EnnoidMe/ENNOID-BMS/Master/LV/PCB/CAD/AMC1301.step

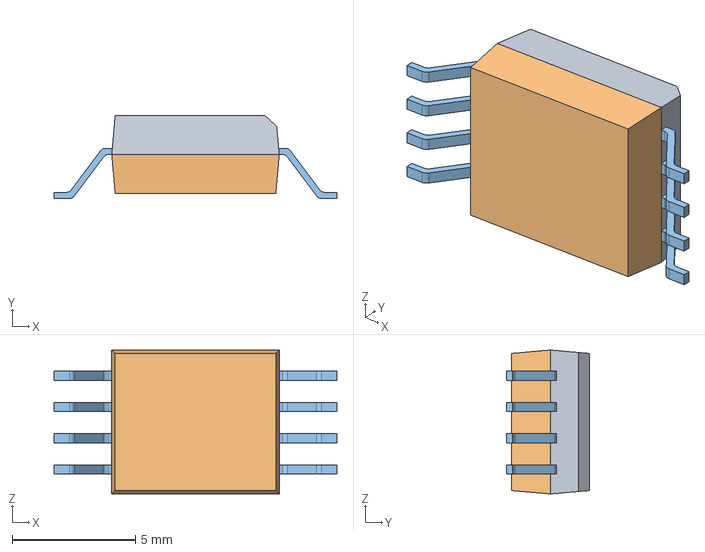
[picture p14: CAD file, 2019-01-14]
Master/LV/PCB/CAD/AMC1301.step
11.5 x 3.38 x 5.85 mm
