EnnoidMe/ENNOID-BMS/Master/LV/PCB/CAD/BAS-M-R0002.step

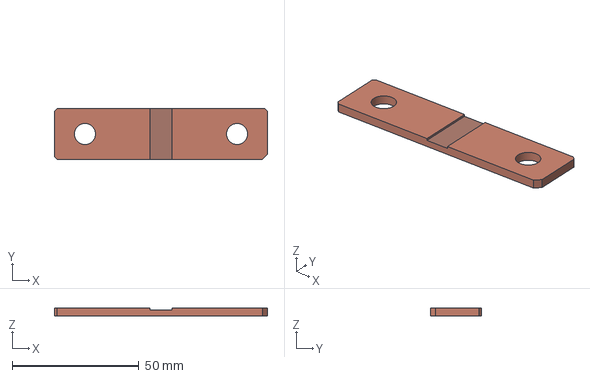
[picture p15: CAD file, 2018-12-30]
Master/LV/PCB/CAD/BAS-M-R0002.step
84.0 x 20.0 x 3.00 mm
