EnnoidMe/ENNOID-BMS/Master/HV/PCB/BMS-Master.sch

## KiCad design Master/HV/PCB/BMS-Master.sch (2020-04-05)

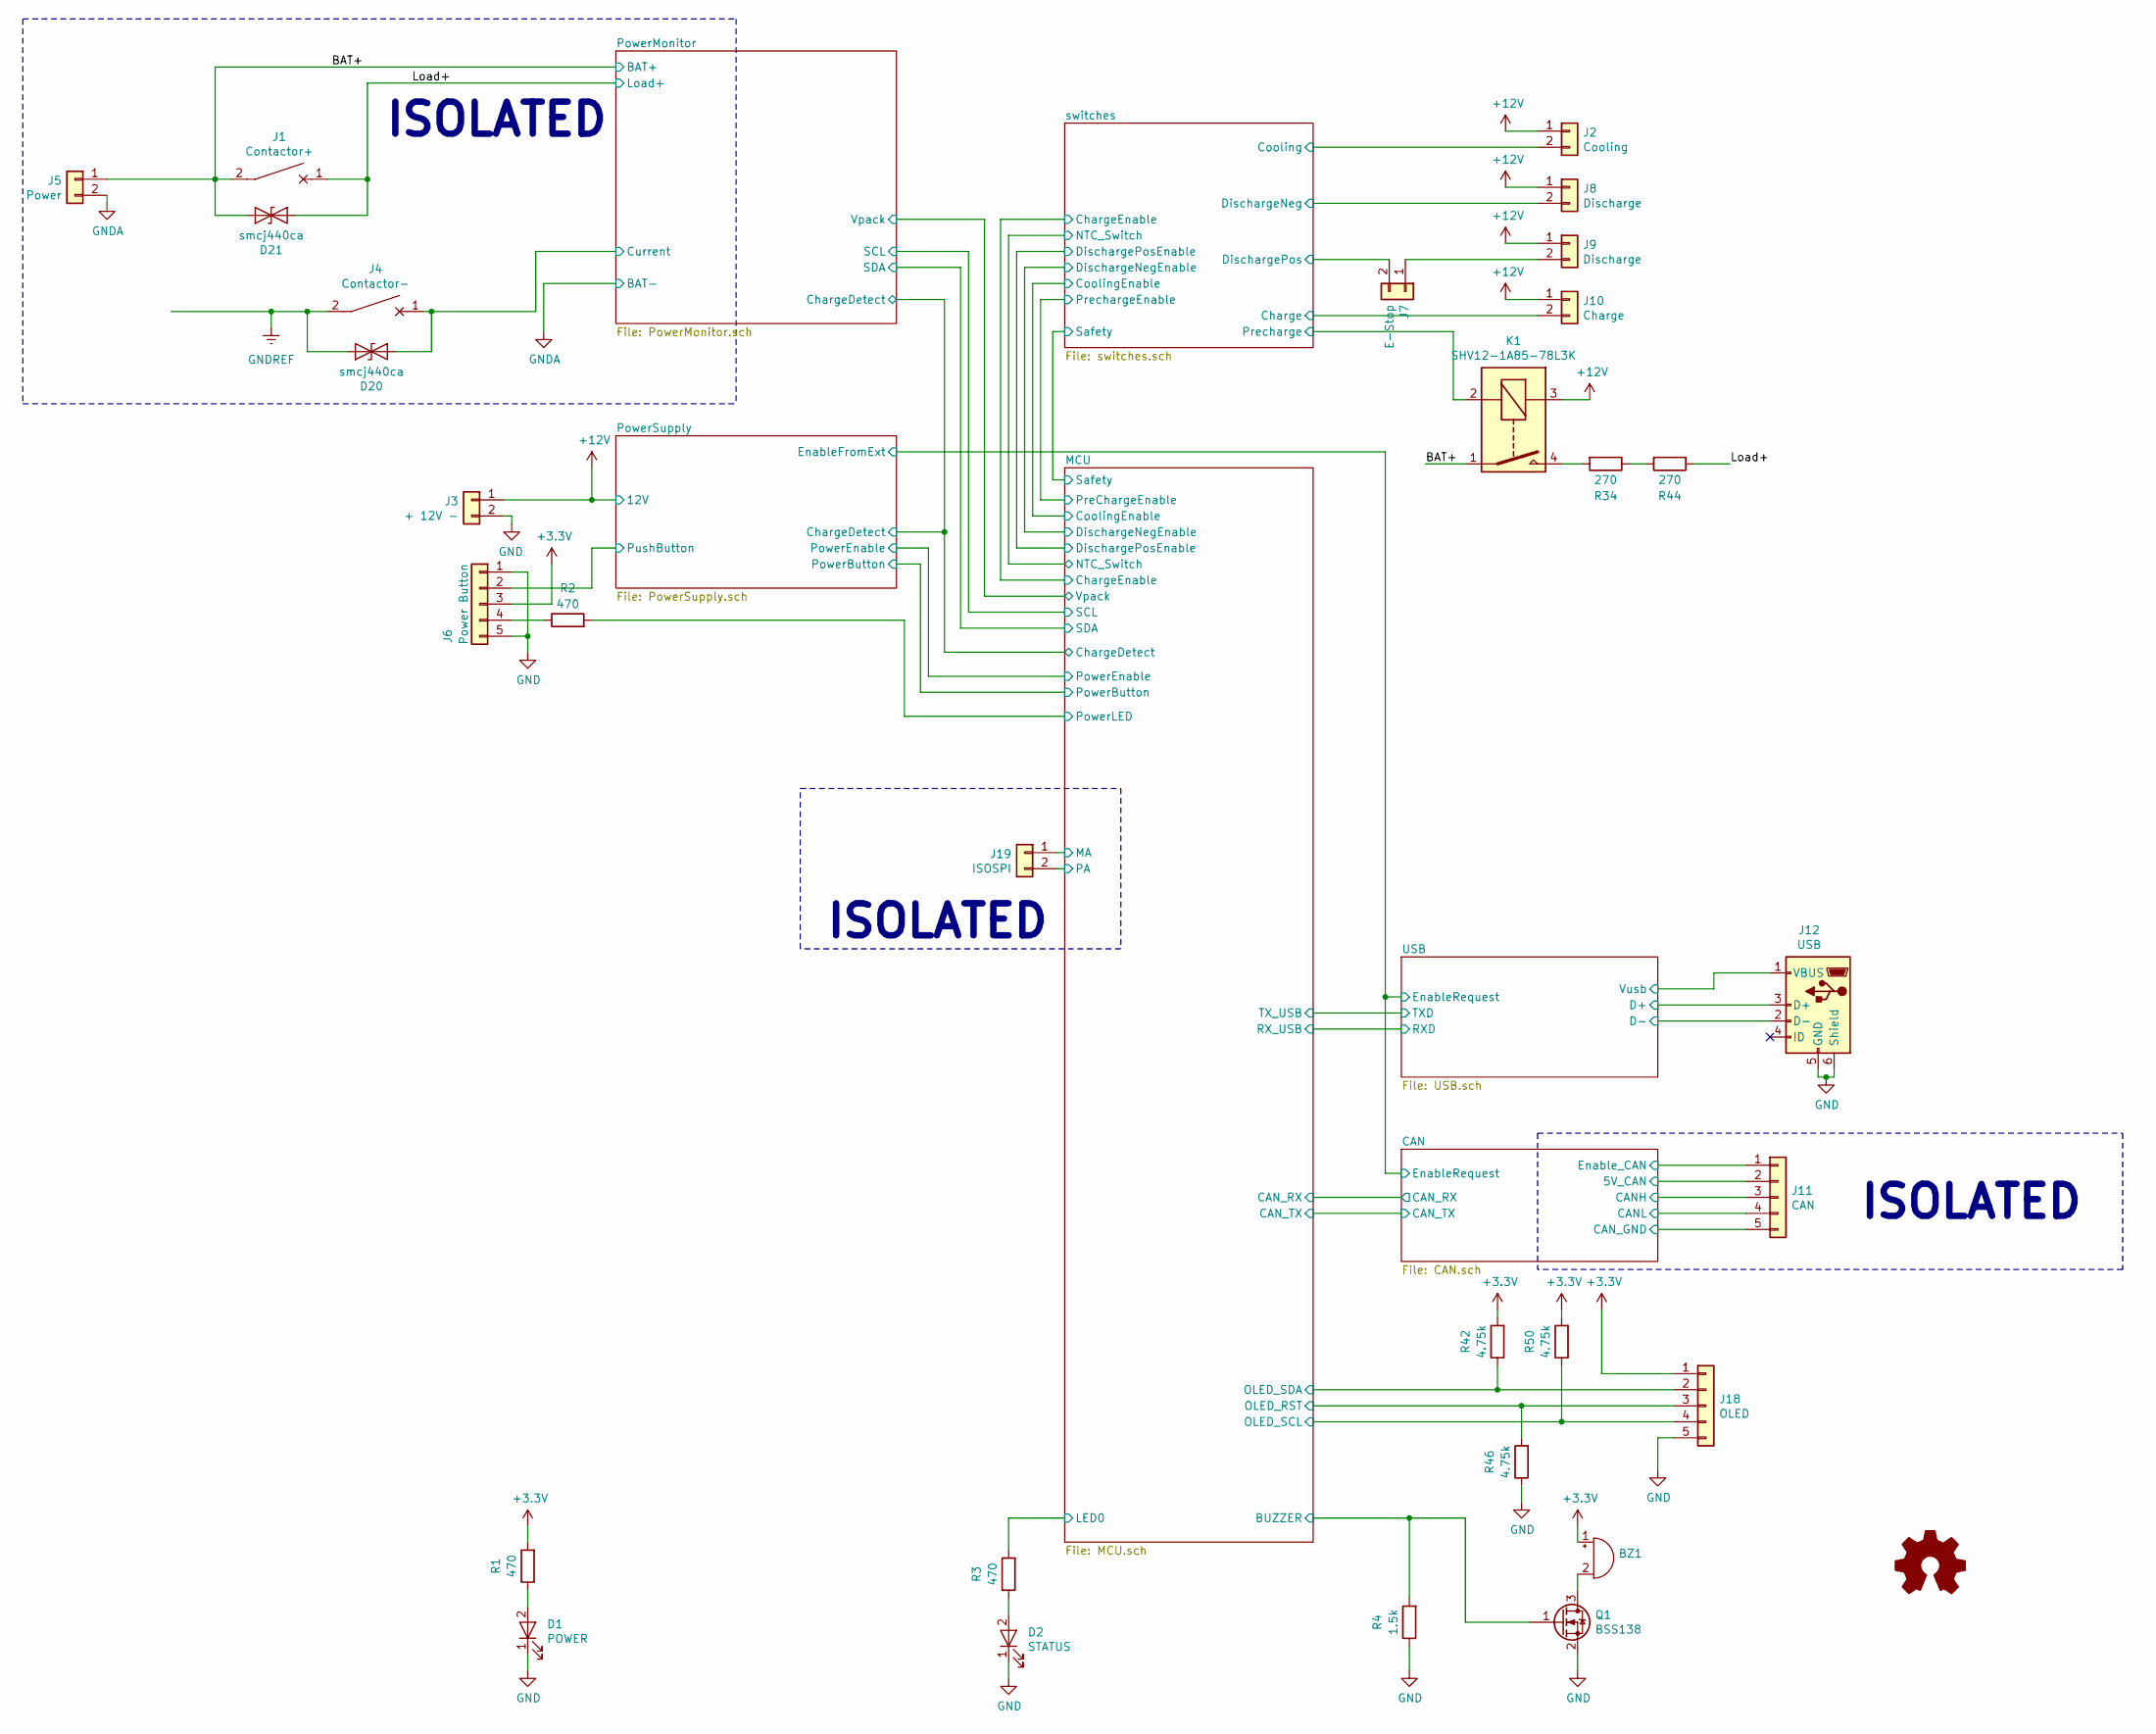
[picture p17: schematic BMS-Master.sch]

Parts:
BZ1: AI-1027-TWT-5V; BUZZER; MPN AI-1027-TWT-5V-2-R
D1: POWER; LED_0603_1608Metric; MPN SML-D12P8WT86C
D2: STATUS; LED_0603_1608Metric; MPN SML-D12P8WT86C
D20, D21: smcj440ca; D_SMC; MPN smcj440ca
J1: Contactor+; EVC500; MPN N/A
J2: Cooling; Pin_1x02-XL; MPN 70543-0001
J3: + 12V -; Pin_1x02-XL; MPN 70543-0001
J4: Contactor-; EVC500; MPN N/A
J5: Power; PhoenixContact_GMSTBVA_2,5_2-G_1x02_P7.50mm_Vertical; MPN 30.102
J6: Power Button; Molex_KK-6410-05_05x2.54mm_Straight; MPN 282834-5
J7: E-Stop; Pin_1x02-XL; MPN 70543-0001
J8, J9: Discharge; Pin_1x02-XL; MPN 70543-0001
J10: Charge; Pin_1x02-XL; MPN 70543-0001
J11: CAN; Molex_KK-6410-05_05x2.54mm_Straight; MPN 70543-0004
J12: USB; USB_Micro-B_Molex-105133-0001; MPN 47346-0001
J18: OLED; Molex_KK-6410-05_05x2.54mm_Straight; MPN 70543-0004
J19: ISOSPI; Pin_1x02-XL; MPN 70543-0001
K1: SHV12-1A85-78L3K; SHV12-1AB5-7BL3K
LOGO1: Logo_Open_Hardware_Small; ENNOID-LOGO; MPN N/A
Q1: BSS138; SOT-23; MPN BSS138
R1, R2, R3: 470; R_0603_1608Metric; MPN RC0603JR-07470RL
R4: 1.5k; R_0603_1608Metric; MPN RC0603JR-071K5L
R34, R44: 270; SM_3; MPN SMW3270RJT
R42, R46, R50: 4.75k; R_0603_1608Metric; MPN RC0603JR-074K7L

Connections:
5V_CAN: J11.2
+3.3V: BZ1.1 (-), J6.3, J18.1, R1.2, R42.2, R50.2
+12V: J2.1, J3.1, J8.1, J9.1, J10.1, K1.3
BAT+: D21.2 (A2), J1.2, J5.1, K1.1
BUZZER: Q1.1 (G), R4.2
CANH: J11.3
CANL: J11.4
CAN_GND: J11.5
Charge: J10.2
Cooling: J2.2
Current: D20.1 (A1), J4.1
D+: J12.3 (D+)
D-: J12.2 (D-)
DischargeNeg: J8.2
DischargePos: J7.2
Enable_CAN: J11.1
GND: D1.1 (K), D2.1 (K), J3.2, J6.1, J6.5, J12.5 (GND), J12.6 (Shield), J18.5, Q1.2 (S), R4.1, R46.1
GNDA: J5.2
GNDREF: D20.2 (A2), J4.2
LED0: R3.2
Load+: D21.1 (A1), J1.1, R44.1
MA: J19.1
unnamed: BZ1.2 (+), Q1.3 (D)
unnamed: D1.2 (A), R1.1
unnamed: D2.2 (A), R3.1
unnamed: J6.4, R2.1
unnamed: J7.1, J9.2
unnamed: K1.4, R34.2
unnamed: R34.1, R44.2
OLED_RST: J18.3, R46.2
OLED_SCL: J18.4, R50.1
OLED_SDA: J18.2, R42.1
PA: J19.2
PowerLED: R2.2
Precharge: K1.2
PushButton: J6.2
Vusb: J12.1 (VBUS)

Notes on the sheet:
ISOLATED
