EnnoidMe/ENNOID-BMS/Master/HV/PCB/MCU.sch

## KiCad design Master/HV/PCB/MCU.sch (2020-03-30)

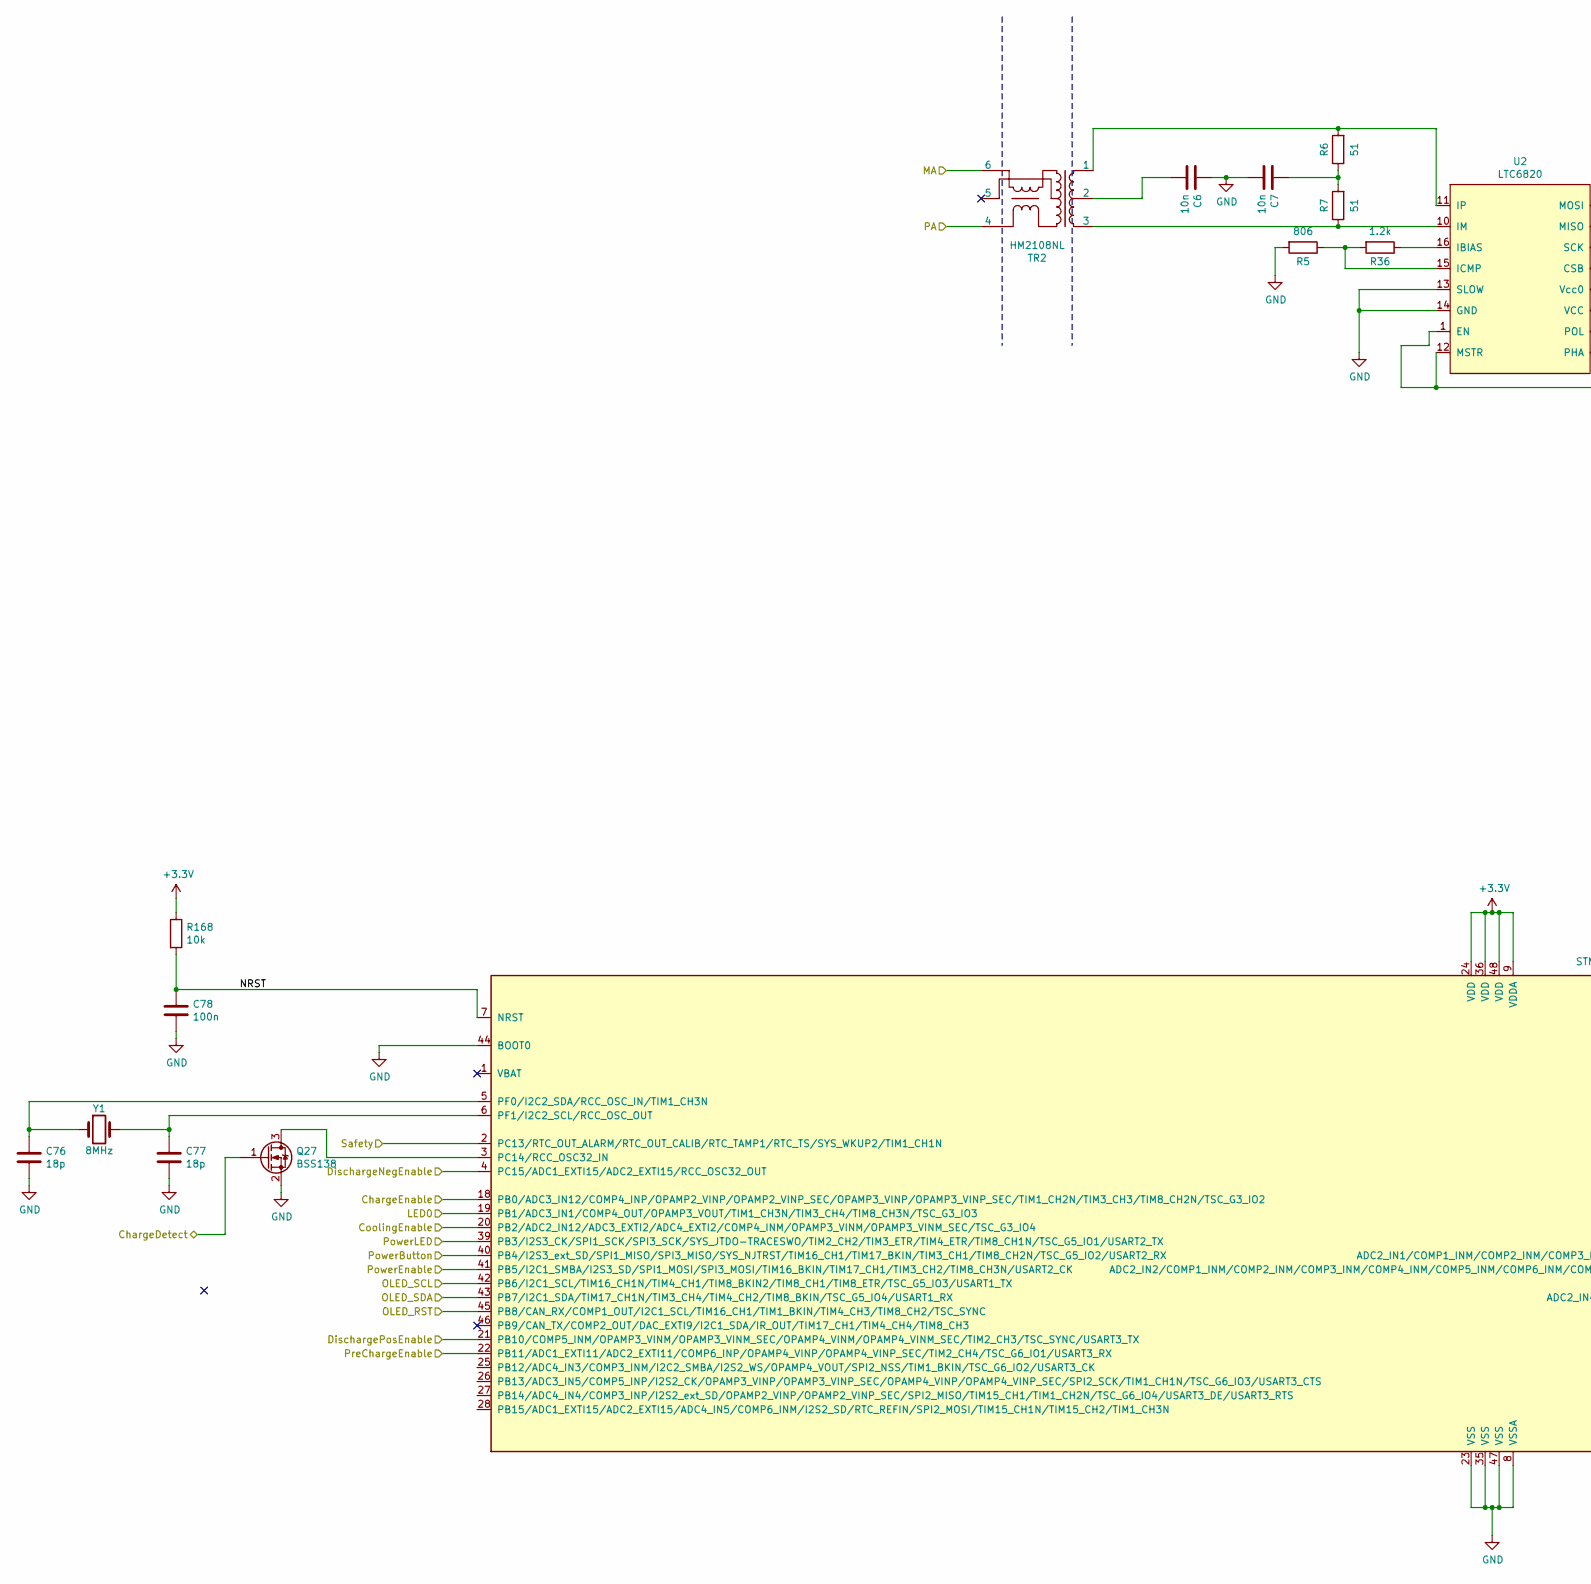
[picture p19: schematic MCU.sch, part in row 1, column 1]

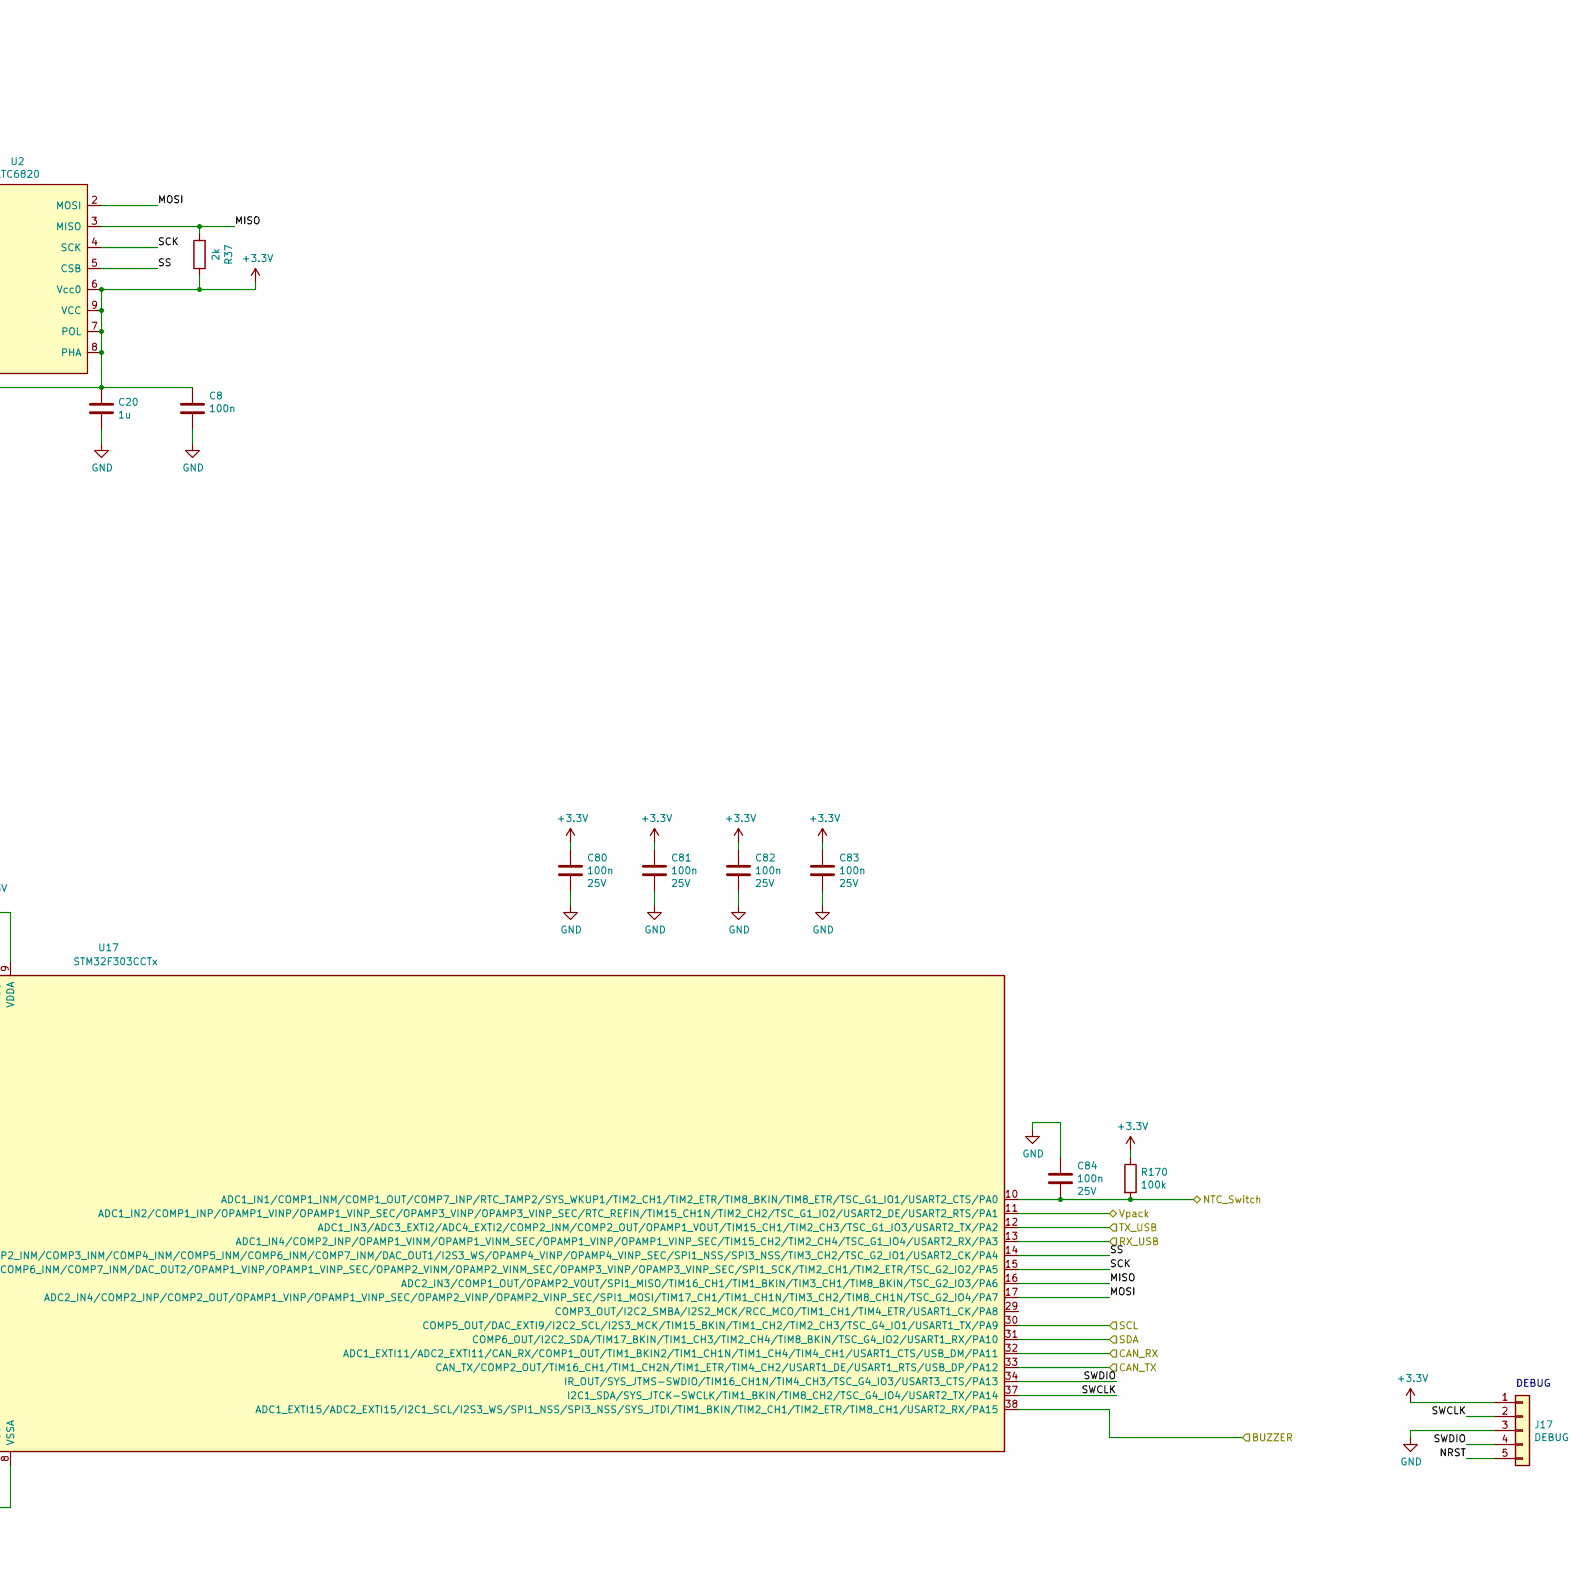
[picture p20: schematic MCU.sch, part in row 1, column 2]

Parts:
C6, C7: 10n; C_0603_1608Metric; MPN GRM188R71H103KA01D
C8, C80, C81, C82, C83, C84: 100n; C_0603_1608Metric; Voltage 25V; MPN GRM188R71E104KA01D
C20: 1u; C_0603_1608Metric; MPN GRM188R71E105KA12D
C76, C77: 18p; C_0603_1608Metric; Voltage 50V; MPN GRM1885C1H180JA01D
C78: 100n; C_0603_1608Metric; MPN GRM188R71E104KA01D
J17: DEBUG; Molex_PicoBlade_53398-0571_1x05-1MP_P1.25mm_Vertical; MPN 53398-0571
Q27: BSS138; SOT-23; MPN BSS138
R5: 806; R_0603_1608Metric; MPN RC0603FR-07806RL
R6, R7: 51; R_0603_1608Metric; MPN RC0603JR-0751RL
R36: 1.2k; R_0603_1608Metric; MPN RC0603JR-071K2L
R37: 2k; R_0603_1608Metric; MPN RC0603FR-072KL
R168: 10k; R_0603_1608Metric; MPN RC0603FR-0710KL
R170: 100k; R_0603_1608Metric; MPN RC0603JR-07100KL
TR2: HM2108NL; MPN HM2108NL
U2: LTC6820; MSOP-16_3x4mm_Pitch0.5mm; MPN LTC6820IMS#PBF
U17: STM32F303CCTx; LQFP-48_7x7mm_Pitch0.5mm; MPN STM32F303CCT6
Y1: 8MHz; Crystal_SMD_Abracon_ABM3-2pin_5.0x3.2mm; MPN ABM3-8.000MHZ-D2Y-T

Connections:
+3.3V: C8.1, C20.2, C80.1, C81.1, C82.1, C83.1, J17.1, R37.1, R168.1, R170.1, U2.1 (EN), U2.6 (Vcc0), U2.7 (POL), U2.8 (PHA), U2.9 (VCC), U2.12 (MSTR), U17.9 (VDDA), U17.24 (VDD), U17.36 (VDD), U17.48 (VDD)
BUZZER: U17.38 (ADC1_EXTI15/ADC2_EXTI15/I2C1_SCL/I2S3_W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)
CAN_RX: U17.32 (ADC1_EXTI11/ADC2_EXTI11/CAN_RX/COMP1_OU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)
CAN_TX: U17.33 (CAN_TX/COMP2_OUT/TIM16_CH1/TIM1_CH2N/TI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)
ChargeDetect: Q27.1 (G)
ChargeEnable: U17.18 (PB0/ADC3_IN12/COMP4_INP/OPAMP2_VINP/OPA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)
CoolingEnable: U17.20 (PB2/ADC2_IN12/ADC3_EXTI2/ADC4_EXTI2/COM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)
DischargeNegEnable: U17.4 (PC15/ADC1_EXTI15/ADC2_EXTI15/RCC_OSC32_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)
DischargePosEnable: U17.21 (PB10/COMP5_INM/OPAMP3_VINM/OPAMP3_VINM_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)
GND: C6.2, C7.1, C8.2, C20.1, C76.2, C77.2, C78.2, C80.2, C81.2, C82.2, C83.2, C84.1, J17.3, Q27.2 (S), R5.2, U2.13 (SLOW), U2.14 (GND), U17.8 (VSSA), U17.23 (VSS), U17.35 (VSS), U17.44 (BOOT0), U17.47 (VSS)
LED0: U17.19 (PB1/ADC3_IN1/COMP4_OUT/OPAMP3_VOUT/TIM1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)
MA: TR2.6
MISO: R37.2, U2.3 (MISO), U17.16 (ADC2_IN3/COMP1_OUT/OPAMP2_VOUT/SPI1_MIS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)
MOSI: U2.2 (MOSI), U17.17 (ADC2_IN4/COMP2_INP/COMP2_OUT/OPAMP1_VIN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)
NRST: C78.1, J17.5, R168.2, U17.7 (NRST)
NTC_Switch: C84.2, R170.2, U17.10 (ADC1_IN1/COMP1_INM/COMP1_OUT/COMP7_INP/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)
unnamed: C6.1, TR2.2
unnamed: C7.2, R6.1, R7.2
unnamed: C76.1, U17.5 (PF0/I2C2_SDA/RCC_OSC_IN/TIM1_CH3N), Y1.1
unnamed: C77.1, U17.6 (PF1/I2C2_SCL/RCC_OSC_OUT), Y1.2
unnamed: Q27.3 (D), U17.3 (PC14/RCC_OSC32_IN)
unnamed: R6.2, TR2.1, U2.11 (IP)
unnamed: R7.1, TR2.3, U2.10 (IM)
unnamed: R36.1, U2.16 (IBIAS)
unnamed: R5.1, R36.2, U2.15 (ICMP)
OLED_RST: U17.45 (PB8/CAN_RX/COMP1_OUT/I2C1_SCL/TIM16_CH1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)
OLED_SCL: U17.42 (PB6/I2C1_SCL/TIM16_CH1N/TIM4_CH1/TIM8_B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)
OLED_SDA: U17.43 (PB7/I2C1_SDA/TIM17_CH1N/TIM3_CH4/TIM4_C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)
PA: TR2.4
PowerButton: U17.40 (PB4/I2S3_ext_SD/SPI1_MISO/SPI3_MISO/SYS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)
PowerEnable: U17.41 (PB5/I2C1_SMBA/I2S3_SD/SPI1_MOSI/SPI3_MO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)
PowerLED: U17.39 (PB3/I2S3_CK/SPI1_SCK/SPI3_SCK/SYS_JTDO-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)
PreChargeEnable: U17.22 (PB11/ADC1_EXTI11/ADC2_EXTI11/COMP6_INP/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)
RX_USB: U17.13 (ADC1_IN4/COMP2_INP/OPAMP1_VINM/OPAMP1_V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)
SCK: U2.4 (SCK), U17.15 (ADC2_IN2/COMP1_INM/COMP2_INM/COMP3_INM/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)
SCL: U17.30 (COMP5_OUT/DAC_EXTI9/I2C2_SCL/I2S3_MCK/T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)
SDA: U17.31 (COMP6_OUT/I2C2_SDA/TIM17_BKIN/TIM1_CH3/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)
SS: U2.5 (CSB), U17.14 (ADC2_IN1/COMP1_INM/COMP2_INM/COMP3_INM/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)
SWCLK: J17.2, U17.37 (I2C1_SDA/SYS_JTCK-SWCLK/TIM1_BKIN/TIM8_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)
SWDIO: J17.4, U17.34 (IR_OUT/SYS_JTMS-SWDIO/TIM16_CH1N/TIM4_C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)
Safety: U17.2 (PC13/RTC_OUT_ALARM/RTC_OUT_CALIB/RTC_TA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)
TX_USB: U17.12 (ADC1_IN3/ADC3_EXTI2/ADC4_EXTI2/COMP2_IN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)
Vpack: U17.11 (ADC1_IN2/COMP1_INP/OPAMP1_VINP/OPAMP1_V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)

Notes on the sheet:
DEBUG
