EnnoidMe/ENNOID-BMS/Master/HV/PCB/PowerMonitor.sch

## KiCad design Master/HV/PCB/PowerMonitor.sch (2020-04-05)

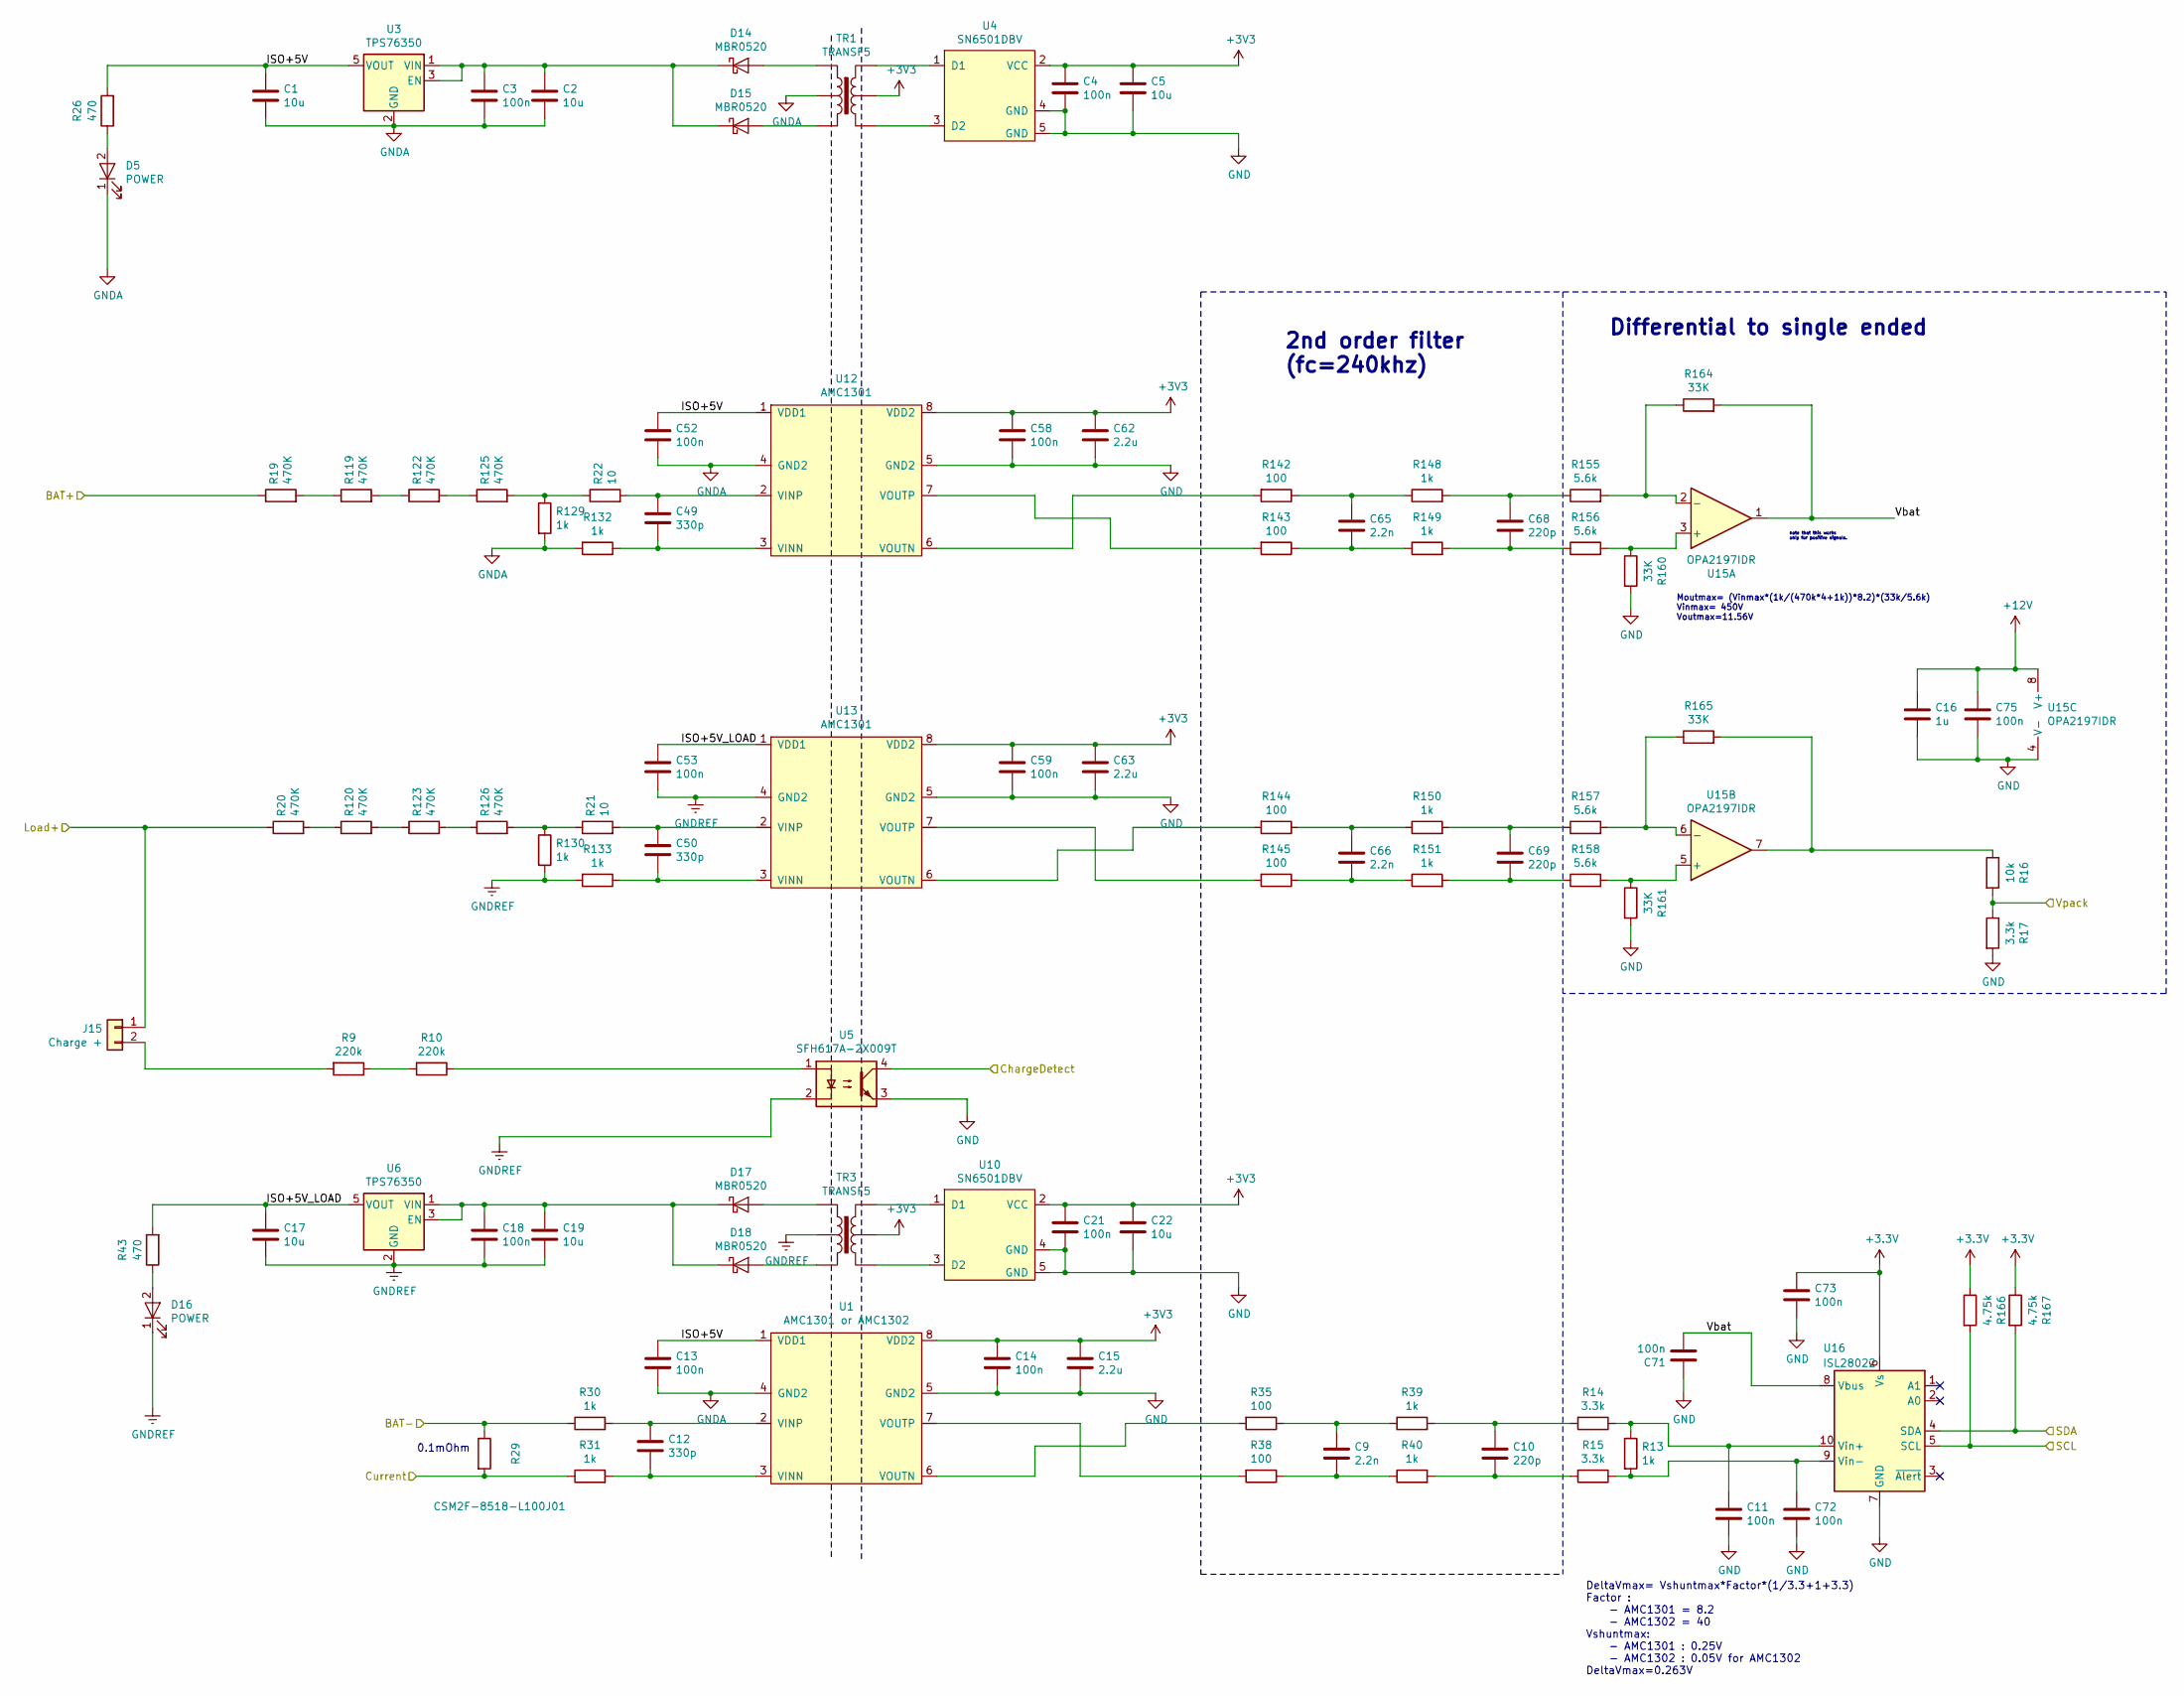
[picture p21: schematic PowerMonitor.sch]

Parts:
C1, C2, C17, C19: 10u; C_0805_2012Metric; MPN CL21A106KAYNNNE
C3, C4, C11, C13, C14, C18, C21, C52, C53, C58, C59, C71, C72, C73, C75: 100n; C_0603_1608Metric; MPN GRM188R71E104KA01D
C5, C22: 10u; C_0603_1608Metric; MPN CL10A106MQ8NNNC
C9, C65, C66: 2.2n; C_0603_1608Metric; MPN GRM1885C1H222JA01D
C10, C68, C69: 220p; C_0603_1608Metric; MPN GRM1555C1H221JA01D
C12, C49, C50: 330p; C_0603_1608Metric; MPN CL10B331KB8NNNC
C15, C62, C63: 2.2u; C_0603_1608Metric; MPN GRM188R61A225KE34D
C16: 1u; C_0603_1608Metric; MPN GRM188R71E105KA12D
D5, D16: POWER; LED_0603_1608Metric; MPN SML-D12P8WT86C
D14, D15, D17, D18: MBR0520; D_SOD-123; MPN MBR0502L
J15: Charge +; PhoenixContact_GMSTBVA_2,5_2-G_1x02_P7.50mm_Vertical; MPN 30.102
R9, R10: 220k; R_2512_6332Metric; MPN 25121WF2203T4E
R13, R30, R31, R39, R40, R129, R130, R132, R133, R148, R149, R150, R151: 1k; R_0603_1608Metric; MPN MCR03EZPFX1001
R14, R15, R17: 3.3k; R_0603_1608Metric; MPN RC0603FR-073K3L
R16: 10k; R_0603_1608Metric; MPN RC0603FR-0710KL
R19, R20, R119, R120, R122, R123, R125, R126: 470K; R_1206_3216Metric; MPN RC1206FR-07470KL
R21, R22: 10; R_0603_1608Metric; MPN RC0603JR-0710RL
R26, R43: 470; R_0603_1608Metric; MPN RC0603JR-07470RL
R29: CSM2F-8518-L100J01; MPN CSM2F-8518-L100J01
R35, R38, R142, R143, R144, R145: 100; R_0603_1608Metric; MPN RC0603FR-07100RL
R155, R156, R157, R158: 5.6k; R_0603_1608Metric; MPN RC0603JR-075K6L
R160, R161, R164, R165: 33K; R_0603_1608Metric; MPN RC0603FR-0733KL
R166, R167: 4.75k; R_0603_1608Metric; MPN RC0603JR-074K7L
TR1, TR3: TRANSF5; WURTH-760390014; MPN 760390014
U1: AMC1301 or AMC1302; SSO-8_6.8x5.9mm_Pitch1.27mm_Clearance8mm; MPN AMC1301DWV
U3, U6: TPS76350; SOT-23-5; MPN TPS76350DBVR
U4, U10: SN6501DBV; SOT-23-5; MPN SN6501DBVR
U5: SFH617A-2X009T; SMDIP-4_W9.53mm_Clearance8mm; MPN SFH617A-2X009T
U12, U13: AMC1301; SSO-8_6.8x5.9mm_Pitch1.27mm_Clearance8mm; MPN AMC1301DWV
U15: OPA2197IDR; SOIC-8_3.9x4.9mm_Pitch1.27mm; MPN OPA2197IDR
U16: ISL28022; MSOP-10_3x3mm_Pitch0.5mm; MPN ISL28022FUZ-T7A

Connections:
+3.3V: C73.2, R166.1, R167.1, U16.6 (Vs)
+3V3: C4.1, C5.1, C14.1, C15.1, C21.1, C22.1, C58.1, C59.1, C62.1, C63.1, TR1.5, TR3.5, U1.8 (VDD2), U4.2 (VCC), U10.2 (VCC), U12.8 (VDD2), U13.8 (VDD2)
+12V: C16.1, C75.1, U15.8 (V+)
BAT+: R19.1
BAT-: R29.1, R30.1
ChargeDetect: U5.4
Current: R29.2, R31.1
GND: C4.2, C5.2, C11.1, C14.2, C15.2, C16.2, C21.2, C22.2, C58.2, C59.2, C62.2, C63.2, C71.2, C72.1, C73.1, C75.2, R17.2, R160.2, R161.2, U1.5 (GND2), U4.4 (GND), U4.5 (GND), U5.3, U10.4 (GND), U10.5 (GND), U12.5 (GND2), U13.5 (GND2), U15.4 (V-), U16.7 (GND)
GNDA: C1.2, C2.2, C3.2, C13.2, C52.2, D5.1 (K), R129.2, R132.2, TR1.2, U1.4 (GND2), U3.2 (GND), U12.4 (GND2)
GNDREF: C17.2, C18.2, C19.2, C53.2, D16.1 (K), R130.2, R133.2, TR3.2, U5.2, U6.2 (GND), U13.4 (GND2)
ISO+5V: C1.1, C13.1, C52.1, R26.2, U1.1 (VDD1), U3.5 (VOUT), U12.1 (VDD1)
ISO+5V_LOAD: C17.1, C53.1, R43.2, U6.5 (VOUT), U13.1 (VDD1)
Load+: J15.1, R20.1
unnamed: C2.1, C3.1, D14.1 (K), D15.1 (K), U3.1 (VIN), U3.3 (EN)
unnamed: C9.1, R35.1, R39.1
unnamed: C9.2, R38.1, R40.1
unnamed: C10.1, R14.2, R39.2
unnamed: C10.2, R15.2, R40.2
unnamed: C11.2, R13.1, R14.1, U16.10 (Vin+)
unnamed: C12.1, R30.2, U1.2 (VINP)
unnamed: C12.2, R31.2, U1.3 (VINN)
unnamed: C18.1, C19.1, D17.1 (K), D18.1 (K), U6.1 (VIN), U6.3 (EN)
unnamed: C49.1, R22.2, U12.2 (VINP)
unnamed: C49.2, R132.1, U12.3 (VINN)
unnamed: C50.1, R21.2, U13.2 (VINP)
unnamed: C50.2, R133.1, U13.3 (VINN)
unnamed: C65.1, R142.1, R148.1
unnamed: C65.2, R143.1, R149.1
unnamed: C66.1, R144.1, R150.1
unnamed: C66.2, R145.1, R151.1
unnamed: C68.1, R148.2, R155.1
unnamed: C68.2, R149.2, R156.1
unnamed: C69.1, R150.2, R157.1
unnamed: C69.2, R151.2, R158.1
unnamed: C72.2, R13.2, R15.1, U16.9 (Vin-)
unnamed: D5.2 (A), R26.1
unnamed: D14.2 (A), TR1.1
unnamed: D15.2 (A), TR1.3
unnamed: D16.2 (A), R43.1
unnamed: D17.2 (A), TR3.1
unnamed: D18.2 (A), TR3.3
unnamed: J15.2, R9.2
unnamed: R10.1, U5.1
unnamed: R9.1, R10.2
unnamed: R16.1, R165.2, U15.7
unnamed: R35.2, U1.6 (VOUTN)
unnamed: R38.2, U1.7 (VOUTP)
unnamed: R19.2, R119.1
unnamed: R119.2, R122.1
unnamed: R20.2, R120.1
unnamed: R120.2, R123.1
unnamed: R122.2, R125.1
unnamed: R123.2, R126.1
unnamed: R22.1, R125.2, R129.1
unnamed: R21.1, R126.2, R130.1
unnamed: R142.2, U12.6 (VOUTN)
unnamed: R143.2, U12.7 (VOUTP)
unnamed: R144.2, U13.6 (VOUTN)
unnamed: R145.2, U13.7 (VOUTP)
unnamed: R155.2, R164.1, U15.2 (-)
unnamed: R156.2, R160.1, U15.3 (+)
unnamed: R157.2, R165.1, U15.6 (-)
unnamed: R158.2, R161.1, U15.5 (+)
unnamed: TR1.4, U4.3 (D2)
unnamed: TR1.6, U4.1 (D1)
unnamed: TR3.4, U10.3 (D2)
unnamed: TR3.6, U10.1 (D1)
SCL: R166.2, U16.5 (SCL)
SDA: R167.2, U16.4 (SDA)
Vbat: C71.1, R164.2, U15.1, U16.8 (Vbus)
Vpack: R16.2, R17.1

Notes on the sheet:
Differential to single ended
note that this works only for positive signals.
2nd order filter (fc=240khz)
0.1mOhm
Moutmax= (Vinmax*(1k/(470k*4+1k))*8.2)*(33k/5.6k) Vinmax= 450V Voutmax=11.56V
DeltaVmax= Vshuntmax*Factor*(1/3.3+1+3.3) Factor : - AMC1301 = 8.2 - AMC1302 = 40 Vshuntmax: - AMC1301 : 0.25V - AMC1302 : 0.05V for AMC1302 DeltaVmax=0.263V
