EnnoidMe/ENNOID-BMS/Master/HV/PCB/PowerSupply.sch

## KiCad design Master/HV/PCB/PowerSupply.sch (2020-03-01)

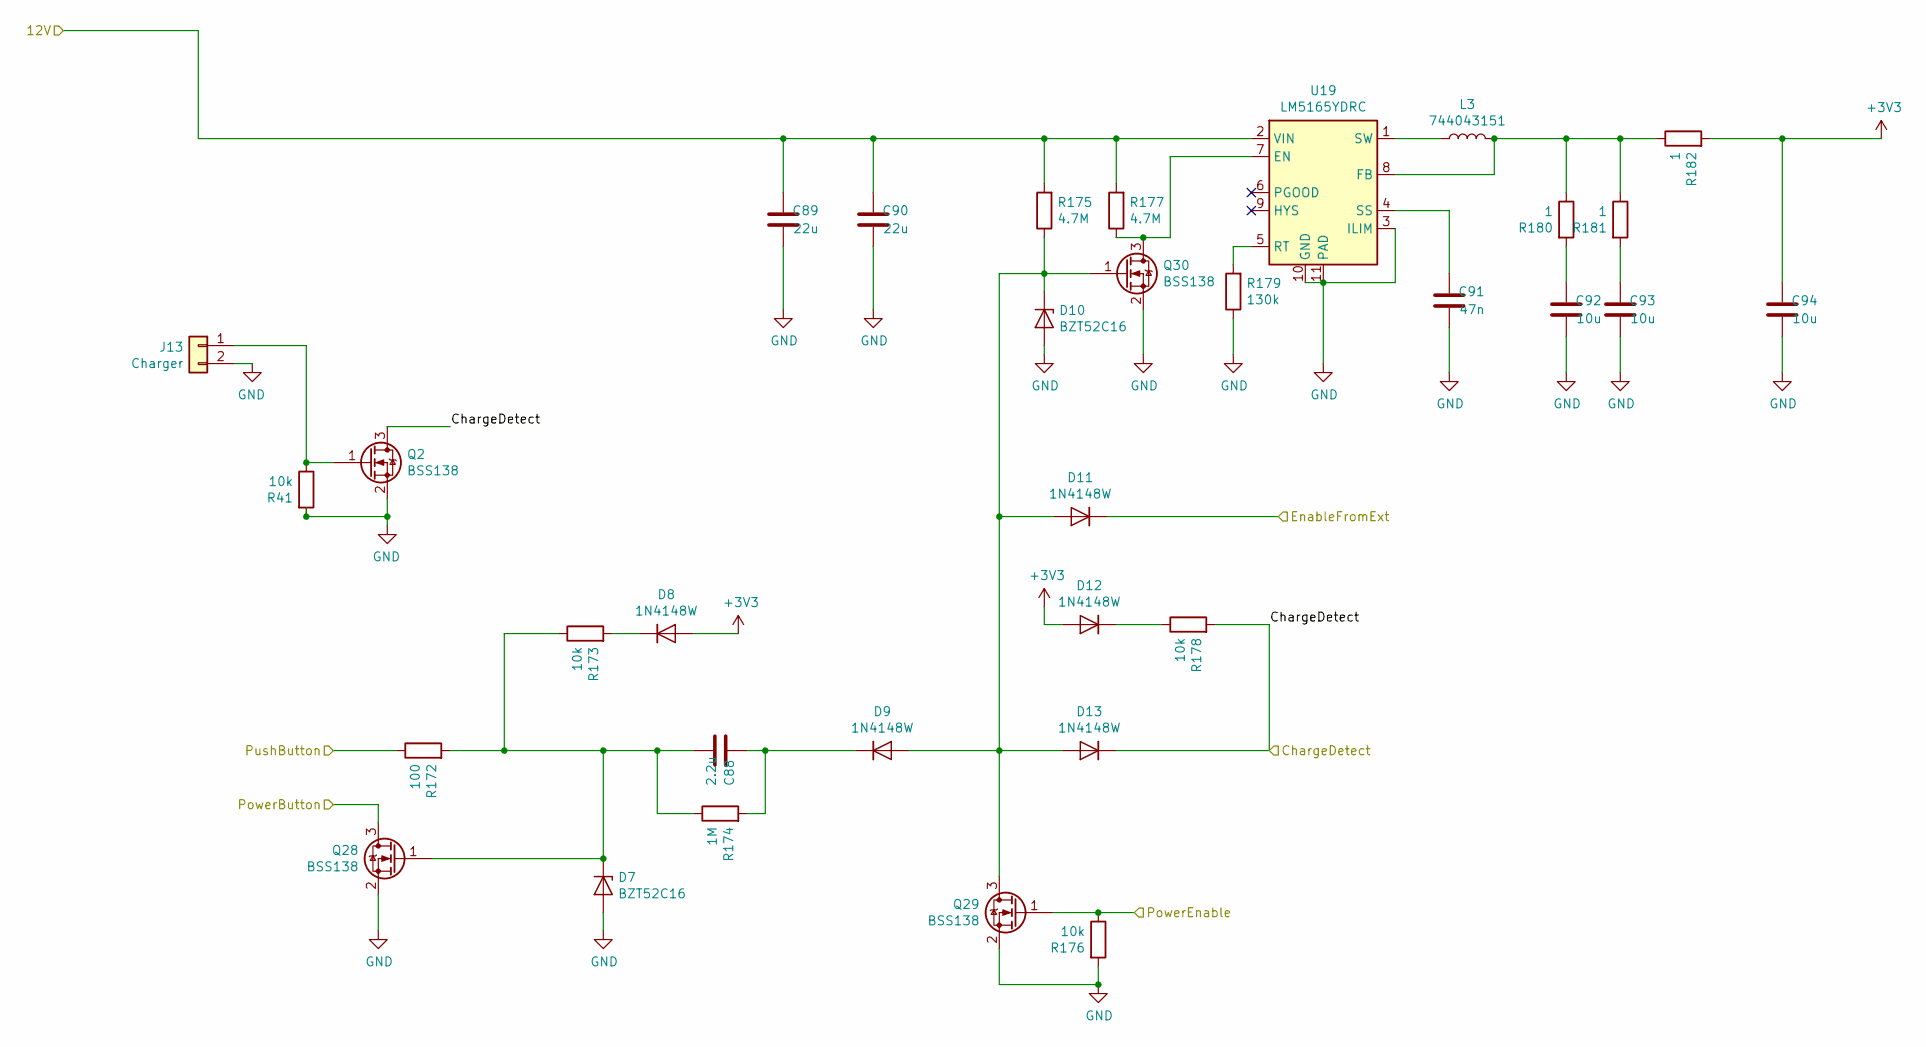
[picture p22: schematic PowerSupply.sch]

Parts:
C88: 2.2u; C_0603_1608Metric; MPN GRM188R61A225KE34D
C89, C90: 22u; C_0805_2012Metric; MPN CL21A226MOQNNNE
C91: 47n; C_0603_1608Metric; Voltage 100V; MPN GCM188R71H473KA55D
C92, C93, C94: 10u; C_0603_1608Metric; MPN CL10A106MQ8NNNC
D7, D10: BZT52C16; D_SOD-123; MPN BZT52C16-E3-08
D8, D9, D11, D12, D13: 1N4148W; D_SOD-123; MPN 1N4148W-7-F
J13: Charger; Pin_1x02-XL; MPN 282834-2
L3: 744043151; L_Wuerth_WE-PD2-Typ-MS; MPN 744043151
Q2, Q28, Q29, Q30: BSS138; SOT-23; MPN BSS138
R41, R173, R176, R178: 10k; R_0603_1608Metric; MPN RC0603FR-0710KL
R172: 100; R_0603_1608Metric; MPN RC0603FR-07100RL
R174: 1M; R_0603_1608Metric; MPN RC0603JR-071ML
R175, R177: 4.7M; R_0603_1608Metric; MPN RC0603FR-074M7L
R179: 130k; R_0603_1608Metric; MPN RC0603FR-07130KL
R180, R181, R182: 1; R_0603_1608Metric; MPN RC0603FR-071RL
U19: LM5165YDRC; Texas_S-PVSON-N10_ThermalVias; MPN LM5165YDRCT

Connections:
12V: C89.2, C90.2, R175.2, R177.2, U19.2 (VIN)
+3V3: C94.2, D8.2 (A), D12.2 (A), R182.2
ChargeDetect: D13.1 (K), Q2.3 (D), R178.2
EnableFromExt: D11.1 (K)
GND: C89.1, C90.1, C91.1, C92.1, C93.1, C94.1, D7.2 (A), D10.2 (A), J13.2, Q2.2 (S), Q28.2 (S), Q29.2 (S), Q30.2 (S), R41.2, R176.2, R179.1, U19.3 (ILIM), U19.10 (GND), U19.11 (PAD)
unnamed: C88.1, D7.1 (K), Q28.1 (G), R172.2, R173.1, R174.1
unnamed: C88.2, D9.1 (K), R174.2
unnamed: C91.2, U19.4 (SS)
unnamed: C92.2, R180.2
unnamed: C93.2, R181.2
unnamed: D8.1 (K), R173.2
unnamed: D9.2 (A), D10.1 (K), D11.2 (A), D13.2 (A), Q29.3 (D), Q30.1 (G), R175.1
unnamed: D12.1 (K), R178.1
unnamed: J13.1, Q2.1 (G), R41.1
unnamed: L3.1, U19.1 (SW)
unnamed: L3.2, R180.1, R181.1, R182.1, U19.8 (FB)
unnamed: Q30.3 (D), R177.1, U19.7 (EN)
unnamed: R179.2, U19.5 (RT)
PowerButton: Q28.3 (D)
PowerEnable: Q29.1 (G), R176.1
PushButton: R172.1
