EnnoidMe/ENNOID-BMS/Master/HV/PCB/USB.sch

## KiCad design Master/HV/PCB/USB.sch (2020-03-30)

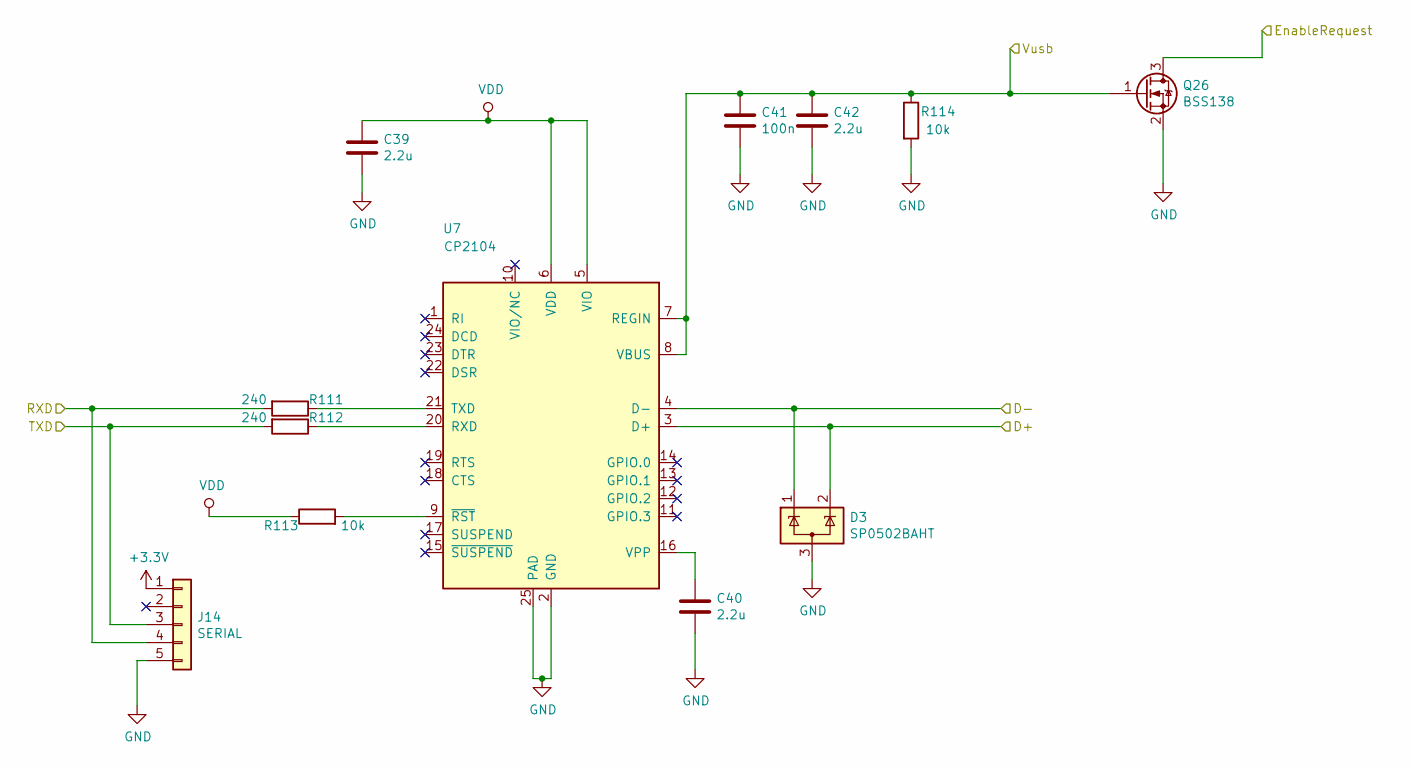
[picture p23: schematic USB.sch]

Parts:
C39, C40, C42: 2.2u; C_0603_1608Metric; MPN GRM188R61A225KE34D
C41: 100n; C_0603_1608Metric; MPN GRM188R71E104KA01D
D3: SP0502BAHT; SOT-23; MPN SP0502BAHTG
J14: SERIAL; Molex_KK-6410-05_05x2.54mm_Straight; MPN 70543-0004
Q26: BSS138; SOT-23; MPN BSS138
R111, R112: 240; R_0603_1608Metric; MPN RC0603FR-07240RL
R113, R114: 10k; R_0603_1608Metric; MPN RC0603FR-0710KL
U7: CP2104; QFN-24-1EP_4x4mm_Pitch0.5mm; MPN CP2104-F03-GM

Connections:
+3.3V: J14.1
D+: D3.2 (K), U7.3 (D+)
D-: D3.1 (K), U7.4 (D-)
EnableRequest: Q26.3 (D)
GND: C39.2, C40.2, C41.2, C42.2, D3.3 (A), J14.5, Q26.2 (S), R114.2, U7.2 (GND), U7.25 (PAD)
unnamed: C40.1, U7.16 (VPP)
unnamed: R111.1, U7.21 (TXD)
unnamed: R112.1, U7.20 (RXD)
unnamed: R113.2, U7.9 (~RST)
RXD: J14.4, R111.2
TXD: J14.3, R112.2
VDD: C39.1, R113.1, U7.5 (VIO), U7.6 (VDD)
Vusb: C41.1, C42.1, Q26.1 (G), R114.1, U7.7 (REGIN), U7.8 (VBUS)
