EnnoidMe/ENNOID-BMS/Master/HV/PCB/cell.sch

## KiCad design Master/HV/PCB/cell.sch (2019-01-11)

Schematic: cell.sch

Parts:
C21: 100n; C_0603_HandSoldering; Voltage 100V
F3: Fuse 0.25A; Fuse_SMD1206_HandSoldering
JP21: Jumper_NC_Dual-Device; Pin_Header_Straight_1x03_Pitch2.54mm
Q25: BSS138; SOT-23
R39: 33; R_2512
R41: R; R_0603_HandSoldering
R48: 100; R_0603_HandSoldering
