EnnoidMe/ENNOID-BMS/Master/HV/PCB/ltc6813.sch

## KiCad design Master/HV/PCB/ltc6813.sch (2019-01-11)

Schematic: ltc6813.sch

Parts:
C15, C18: 100nF; C_0603_HandSoldering; Voltage 100V
C16, C17, C19: 1uF; C_0603_HandSoldering
C97, C98: 100p; C_0603_HandSoldering
JP1, JP2: Jumper_NC_Dual; Pin_Header_Straight_1x03_Pitch2.54mm
Q7: DZT5551; SOT-223-3_TabPin2
R29, R30, R32, R34, R35: 100; R_0603_HandSoldering
R31, R33: 1k; R_0603_HandSoldering
TR1: HM2102NL
U5: LTC6813; TQFP-64-1EP_10x10mm_Pitch0.5mm
