EnnoidMe/ENNOID-BMS/Master/HV/PCB/switches.sch

## KiCad design Master/HV/PCB/switches.sch (2020-03-01)

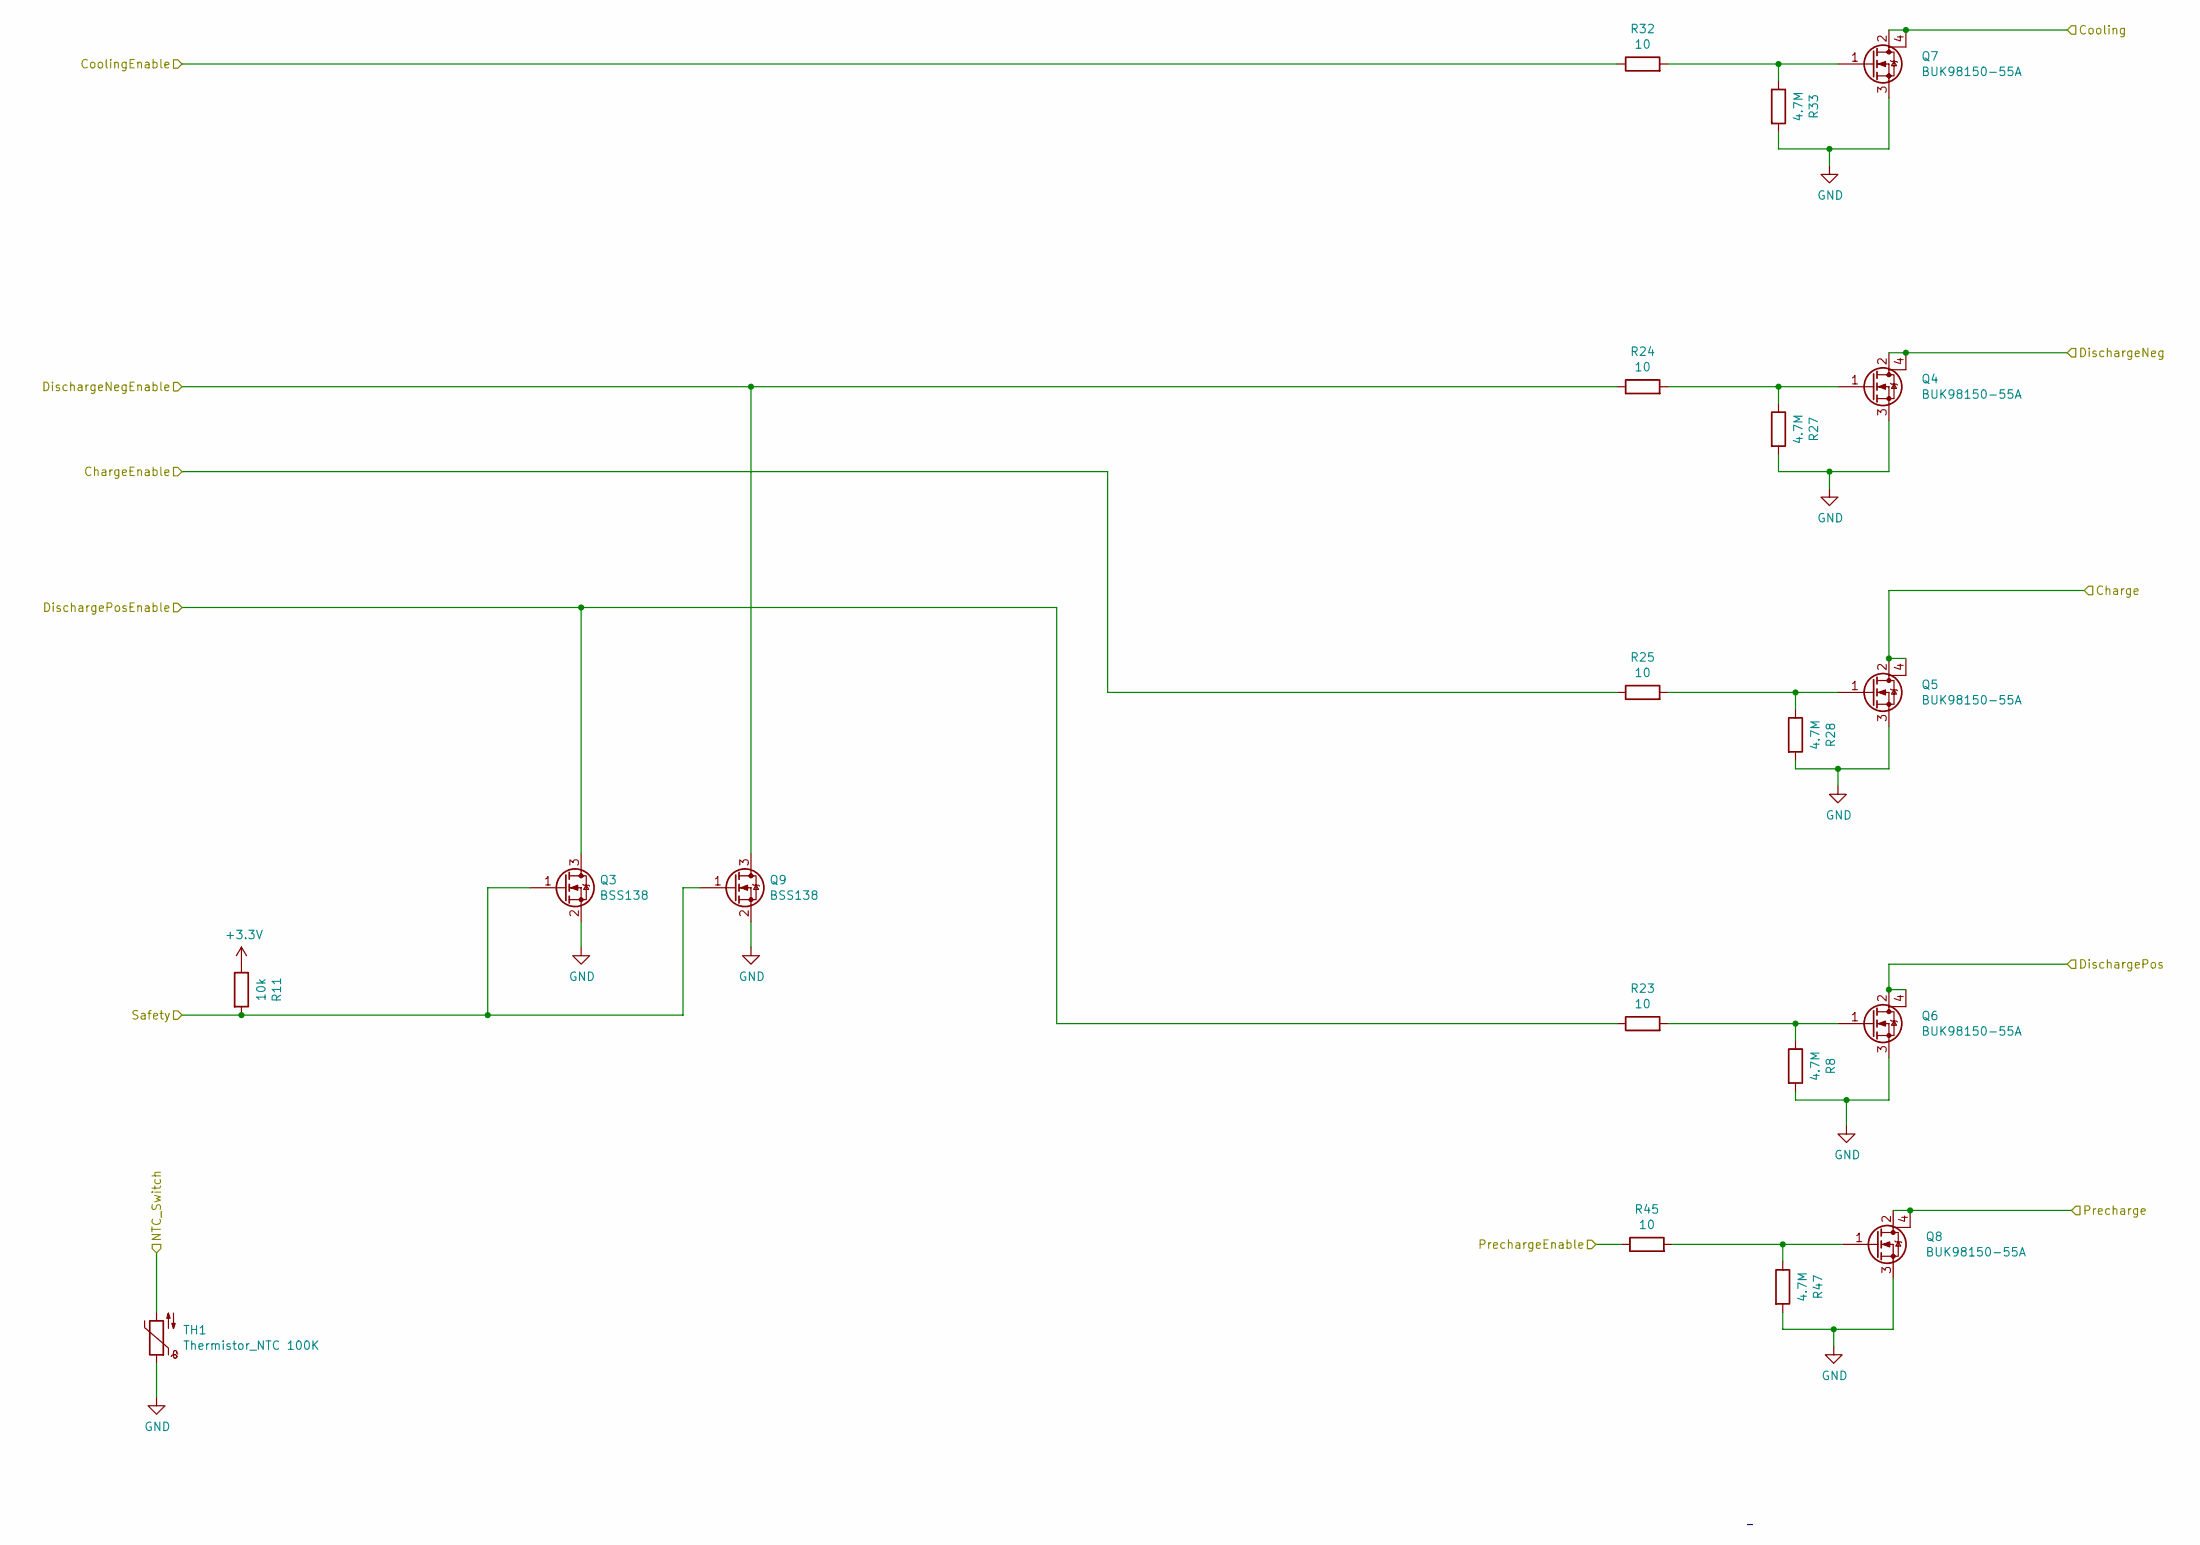
[picture p24: schematic switches.sch]

Parts:
Q3, Q9: BSS138; SOT-23; MPN BSS138
Q4, Q5, Q6, Q7, Q8: BUK98150-55A; SOT-223; MPN BUK98150-55A/CUF
R8, R27, R28, R33, R47: 4.7M; R_0603_1608Metric; MPN RC0603FR-074M7L
R11: 10k; R_0603_1608Metric; MPN RC0603FR-0710KL
R23, R24, R25, R32, R45: 10; R_0603_1608Metric; MPN RC0603JR-0710RL
TH1: Thermistor_NTC 100K; R_0805_2012Metric; MPN SDNT2012X104F4250FTF

Connections:
+3.3V: R11.1
Charge: Q5.2 (D), Q5.4 (D)
ChargeEnable: R25.1
Cooling: Q7.2 (D), Q7.4 (D)
CoolingEnable: R32.1
DischargeNeg: Q4.2 (D), Q4.4 (D)
DischargeNegEnable: Q9.3 (D), R24.1
DischargePos: Q6.2 (D), Q6.4 (D)
DischargePosEnable: Q3.3 (D), R23.1
GND: Q3.2 (S), Q4.3 (S), Q5.3 (S), Q6.3 (S), Q7.3 (S), Q8.3 (S), Q9.2 (S), R8.2, R27.2, R28.2, R33.2, R47.2, TH1.1
NTC_Switch: TH1.2
unnamed: Q4.1 (G), R24.2, R27.1
unnamed: Q5.1 (G), R25.2, R28.1
unnamed: Q6.1 (G), R8.1, R23.2
unnamed: Q7.1 (G), R32.2, R33.1
unnamed: Q8.1 (G), R45.2, R47.1
Precharge: Q8.2 (D), Q8.4 (D)
PrechargeEnable: R45.1
Safety: Q3.1 (G), Q9.1 (G), R11.2
