EnnoidMe/ENNOID-BMS/Master/LV/PCB/BMS-Master-LV.sch

## KiCad design Master/LV/PCB/BMS-Master-LV.sch (2020-03-31)

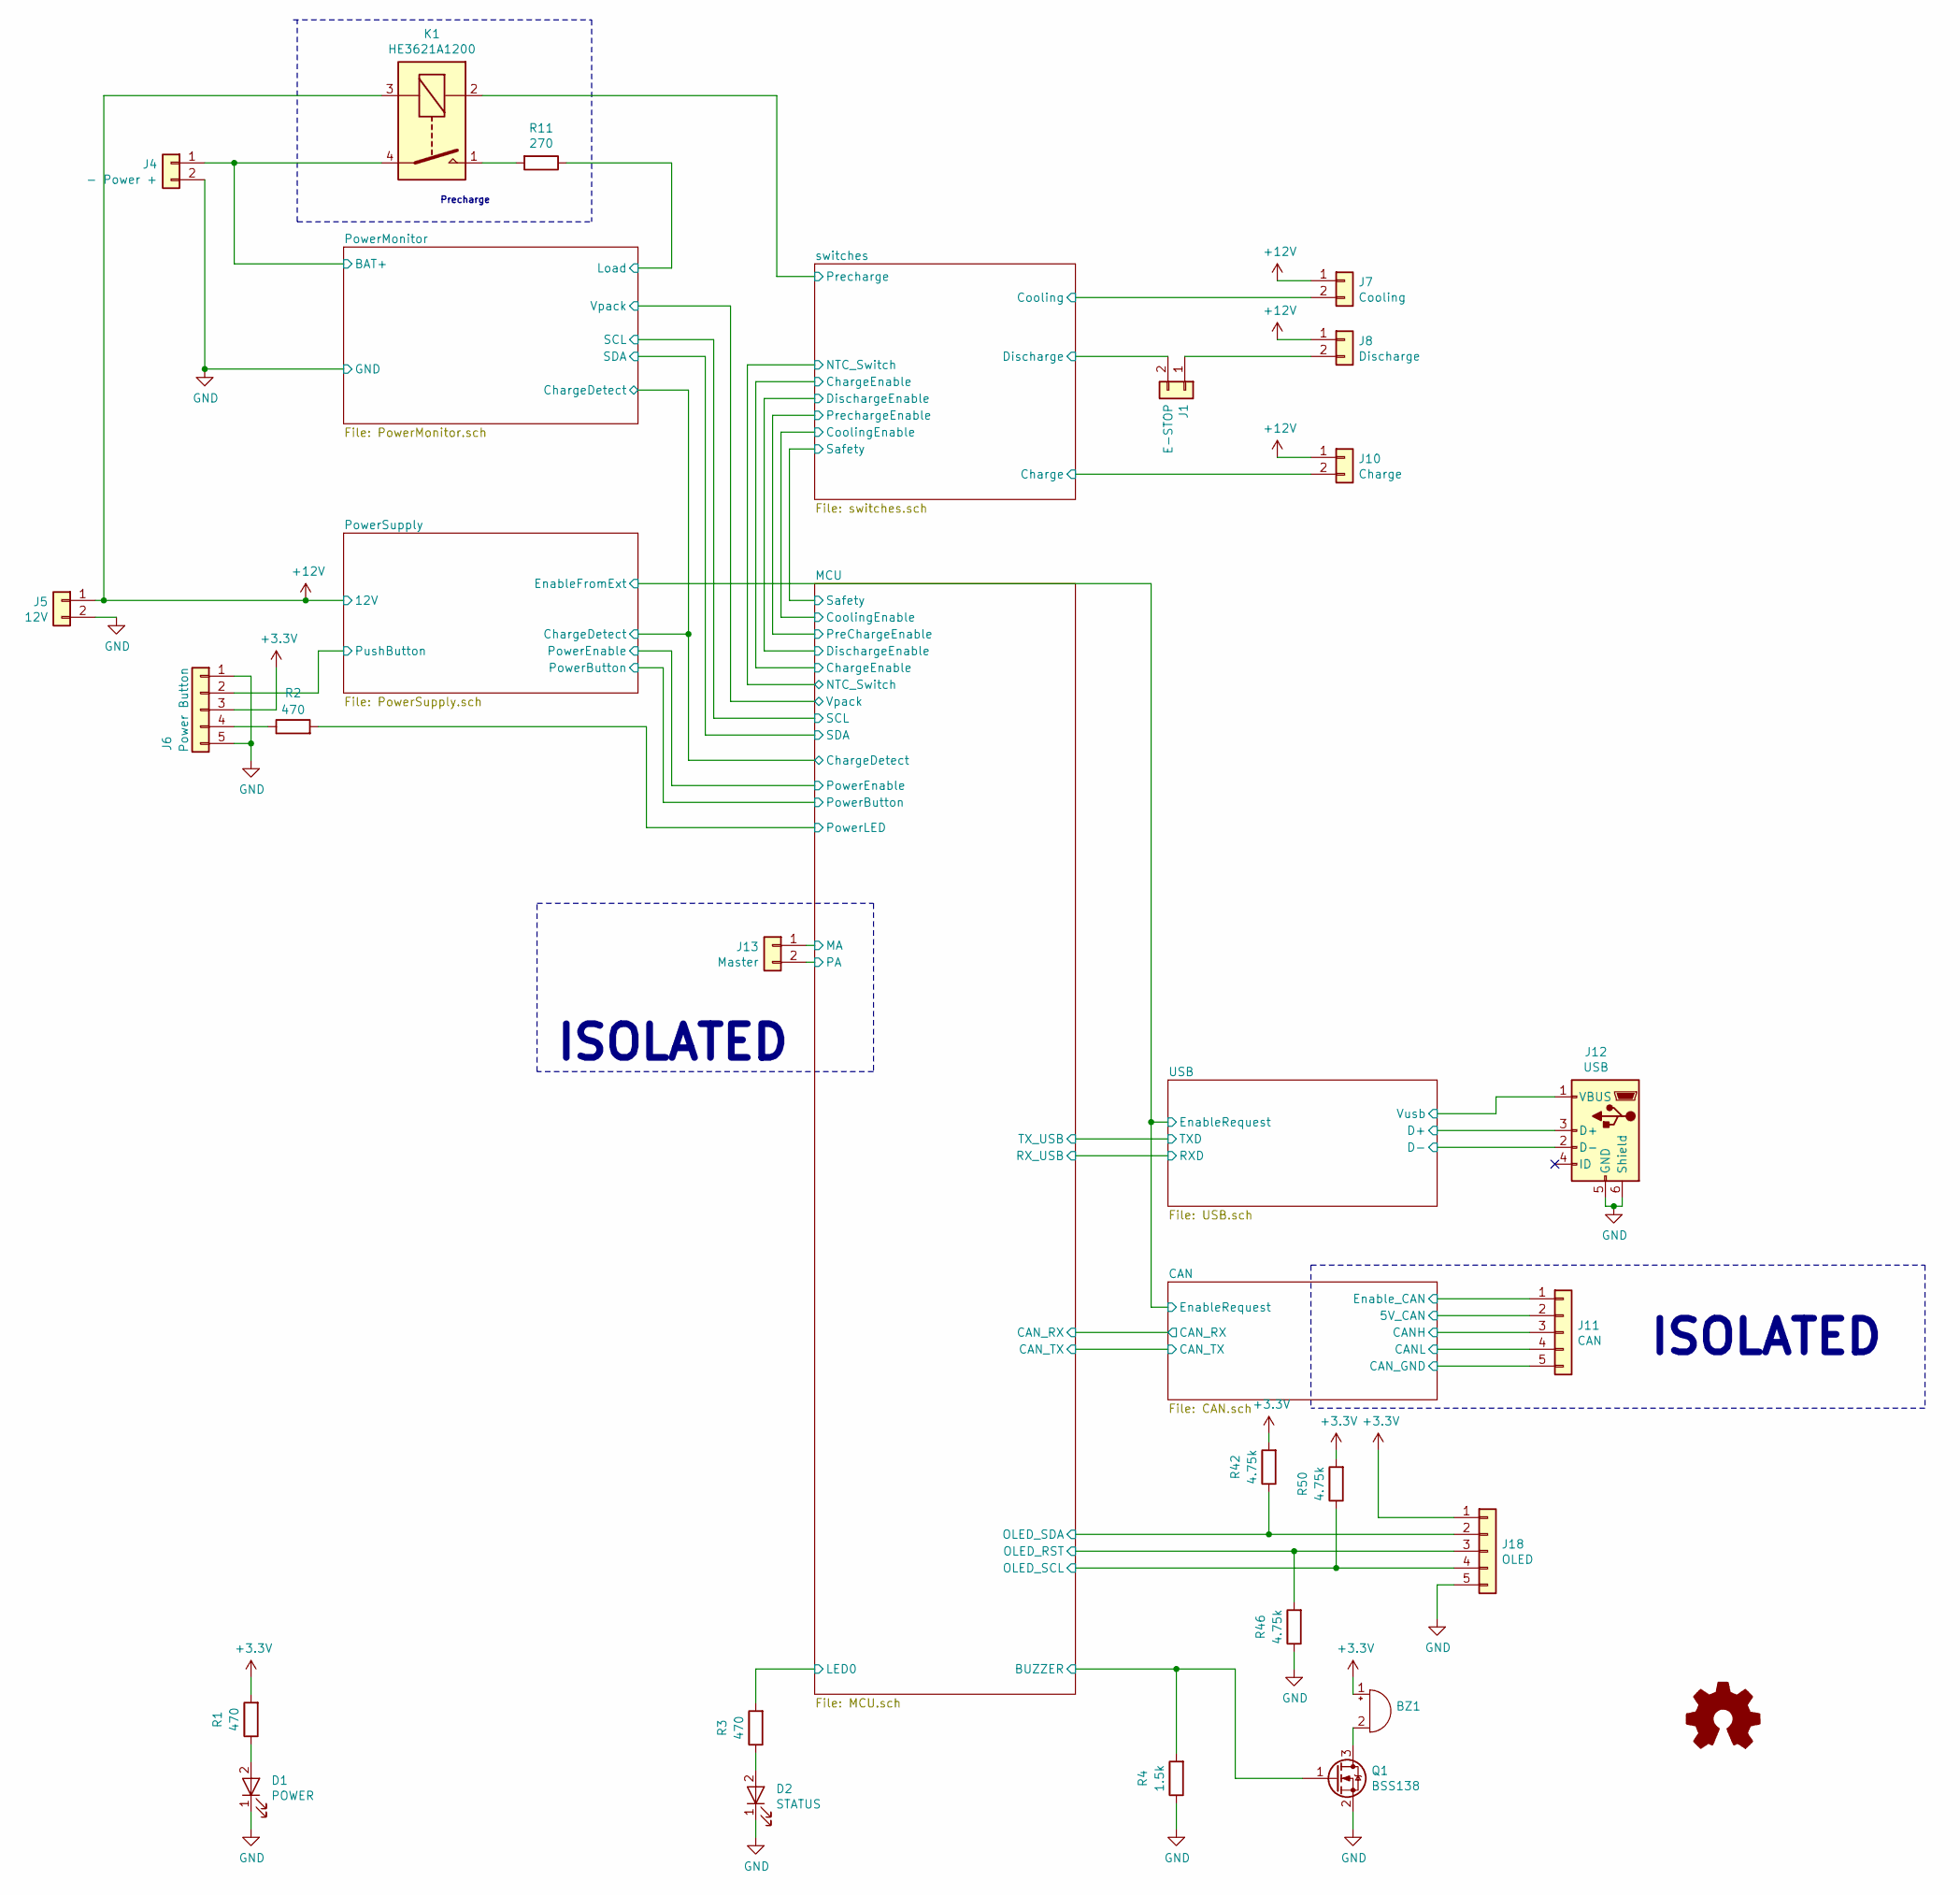
[picture p25: schematic BMS-Master-LV.sch]

Parts:
BZ1: AI-1027-TWT-5V; BUZZER; MPN AI-1027-TWT-5V-2-R
D1: POWER; LED_0603_1608Metric; MPN SML-D12P8WT86C
D2: STATUS; LED_0603_1608Metric; MPN SML-D12P8WT86C
J1: E-STOP; Pin_1x02-XL; MPN 70543-0001
J4: - Power +; PhoenixContact_MCV_1,5_2-G-5.08_1x02_P5.08mm_Vertical; MPN 30.102
J5: 12V; Pin_1x02-XL; MPN 70543-0001
J6: Power Button; Molex_KK-6410-05_05x2.54mm_Straight; MPN 70543-0004
J7: Cooling; Pin_1x02-XL; MPN 70543-0001
J8: Discharge; Pin_1x02-XL; MPN 70543-0001
J10: Charge; Pin_1x02-XL; MPN 70543-0001
J11: CAN; Molex_KK-6410-05_05x2.54mm_Straight; MPN 70543-0004
J12: USB; USB_Micro-B_Molex-105133-0001; MPN 47346-0001
J13: Master; Pin_1x02-XL; MPN 70543-0001
J18: OLED; Molex_KK-6410-05_05x2.54mm_Straight; MPN 70543-0004
K1: HE3621A1200; MPN HE3621A1200
LOGO1: Logo_Open_Hardware_Small; ENNOID-LOGO; MPN N/A
Q1: BSS138; SOT-23; MPN BSS138
R1, R2, R3: 470; R_0603_1608Metric; MPN RC0603JR-07470RL
R4: 1.5k; R_0603_1608Metric; MPN RC0603JR-071K5L
R11: 270; SM_3; MPN SMW3270RJT
R42, R46, R50: 4.75k; R_0603_1608Metric; MPN RC0603JR-074K7L

Connections:
5V_CAN: J11.2
+3.3V: BZ1.1 (-), J6.3, J18.1, R1.2, R42.2, R50.2
+12V: J5.1, J7.1, J8.1, J10.1, K1.3
BAT+: J4.1, K1.4
BUZZER: Q1.1 (G), R4.2
CANH: J11.3
CANL: J11.4
CAN_GND: J11.5
Charge: J10.2
Cooling: J7.2
D+: J12.3 (D+)
D-: J12.2 (D-)
Discharge: J1.2
Enable_CAN: J11.1
GND: D1.1 (K), D2.1 (K), J4.2, J5.2, J6.1, J6.5, J12.5 (GND), J12.6 (Shield), J18.5, Q1.2 (S), R4.1, R46.1
LED0: R3.2
Load: R11.1
MA: J13.1
unnamed: BZ1.2 (+), Q1.3 (D)
unnamed: D1.2 (A), R1.1
unnamed: D2.2 (A), R3.1
unnamed: J1.1, J8.2
unnamed: J6.4, R2.1
unnamed: K1.1, R11.2
OLED_RST: J18.3, R46.2
OLED_SCL: J18.4, R50.1
OLED_SDA: J18.2, R42.1
PA: J13.2
PowerLED: R2.2
Precharge: K1.2
PushButton: J6.2
Vusb: J12.1 (VBUS)

Notes on the sheet:
ISOLATED
Precharge
