EnnoidMe/ENNOID-BMS/Master/LV/PCB/CAN.sch

## KiCad design Master/LV/PCB/CAN.sch (2019-11-12)

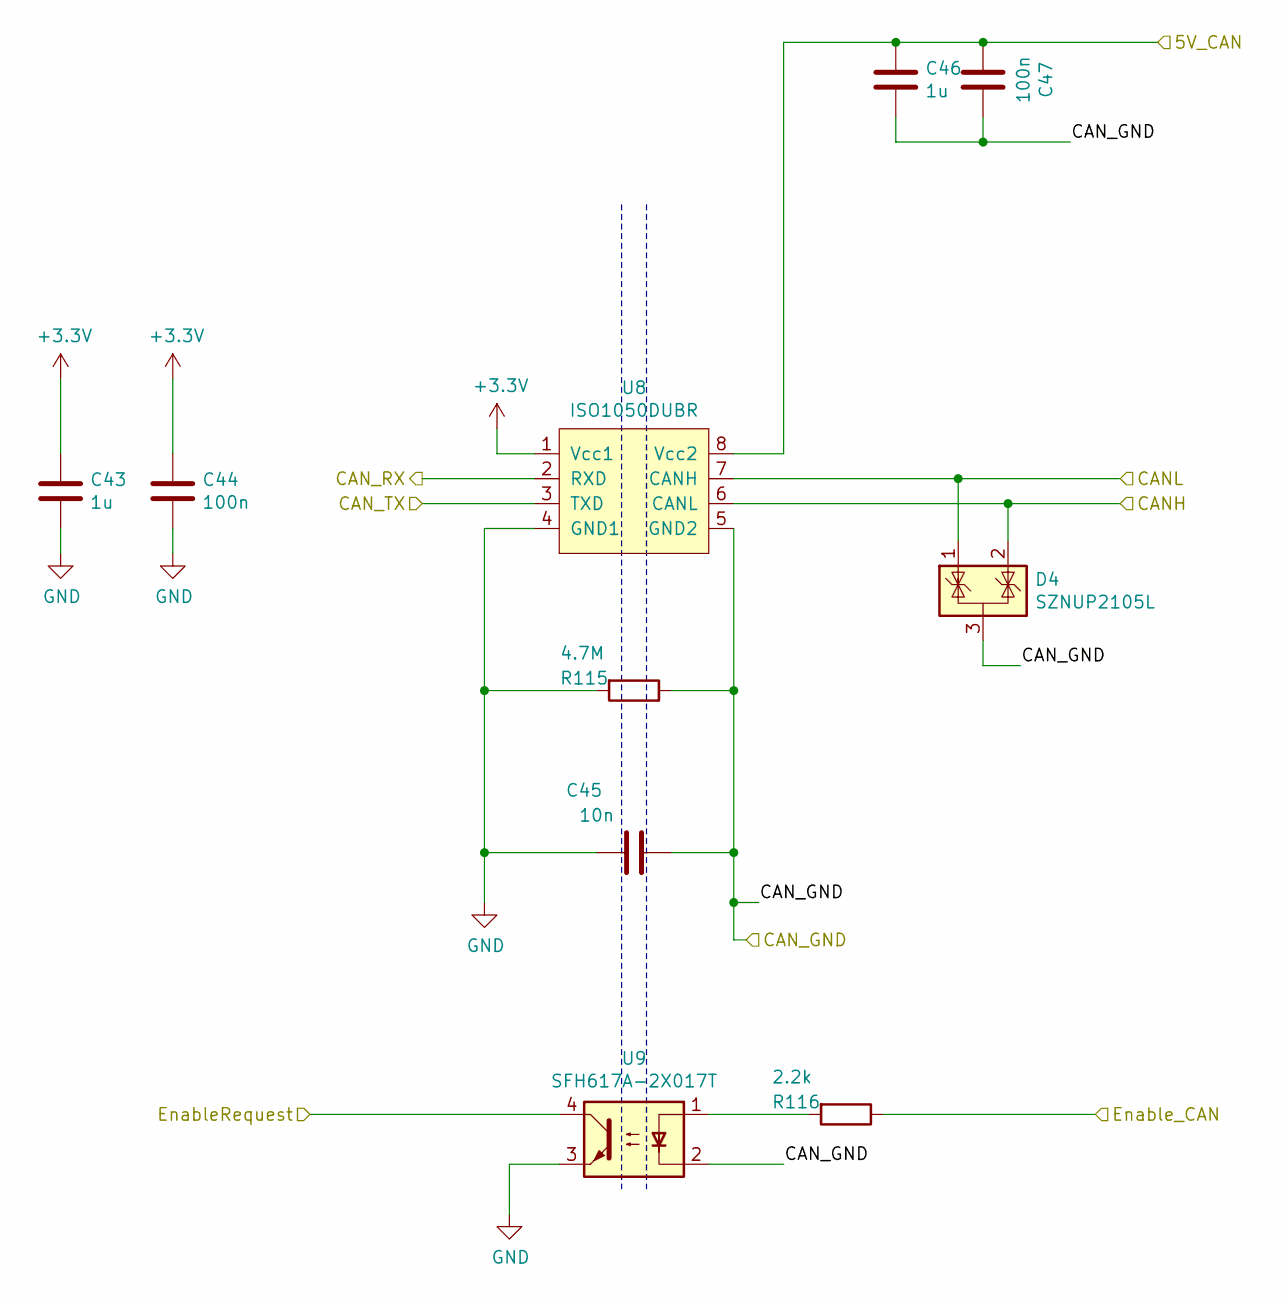
[picture p26: schematic CAN.sch]

Parts:
C43, C46: 1u; C_0805_2012Metric; MPN GRM188R71E105KA12D
C44, C47: 100n; C_0603_1608Metric; MPN GRM188R71E104KA01D
C45: 10n; C_0805_2012Metric; Voltage 100V; MPN GRM188R71H103KA01D
D4: SZNUP2105L; SOT-23; MPN SZNUP2105LT1G
R115: 4.7M; R_0805_2012Metric; Voltage 100V; MPN RC0805JR-0710ML
R116: 2.2k; R_0603_1608Metric; Voltage 100V; MPN RC0603JR-072K2L
U8: ISO1050DUBR; ISO1050; MPN ISO1050DUBR
U9: SFH617A-2X017T; SMDIP-4_W9.53mm_Clearance8mm; MPN SFH617A-2X009T

Connections:
5V_CAN: C46.1, C47.2, U8.8 (Vcc2)
+3.3V: C43.1, C44.1, U8.1 (Vcc1)
CANH: D4.2 (K), U8.6 (CANL)
CANL: D4.1 (K), U8.7 (CANH)
CAN_GND: C45.1, C46.2, C47.1, D4.3 (A), R115.1, U8.5 (GND2), U9.2
CAN_RX: U8.2 (RXD)
CAN_TX: U8.3 (TXD)
EnableRequest: U9.4
Enable_CAN: R116.1
GND: C43.2, C44.2, C45.2, R115.2, U8.4 (GND1), U9.3
unnamed: R116.2, U9.1
