EnnoidMe/ENNOID-BMS/Master/LV/PCB/PowerMonitor.sch

## KiCad design Master/LV/PCB/PowerMonitor.sch (2020-04-05)

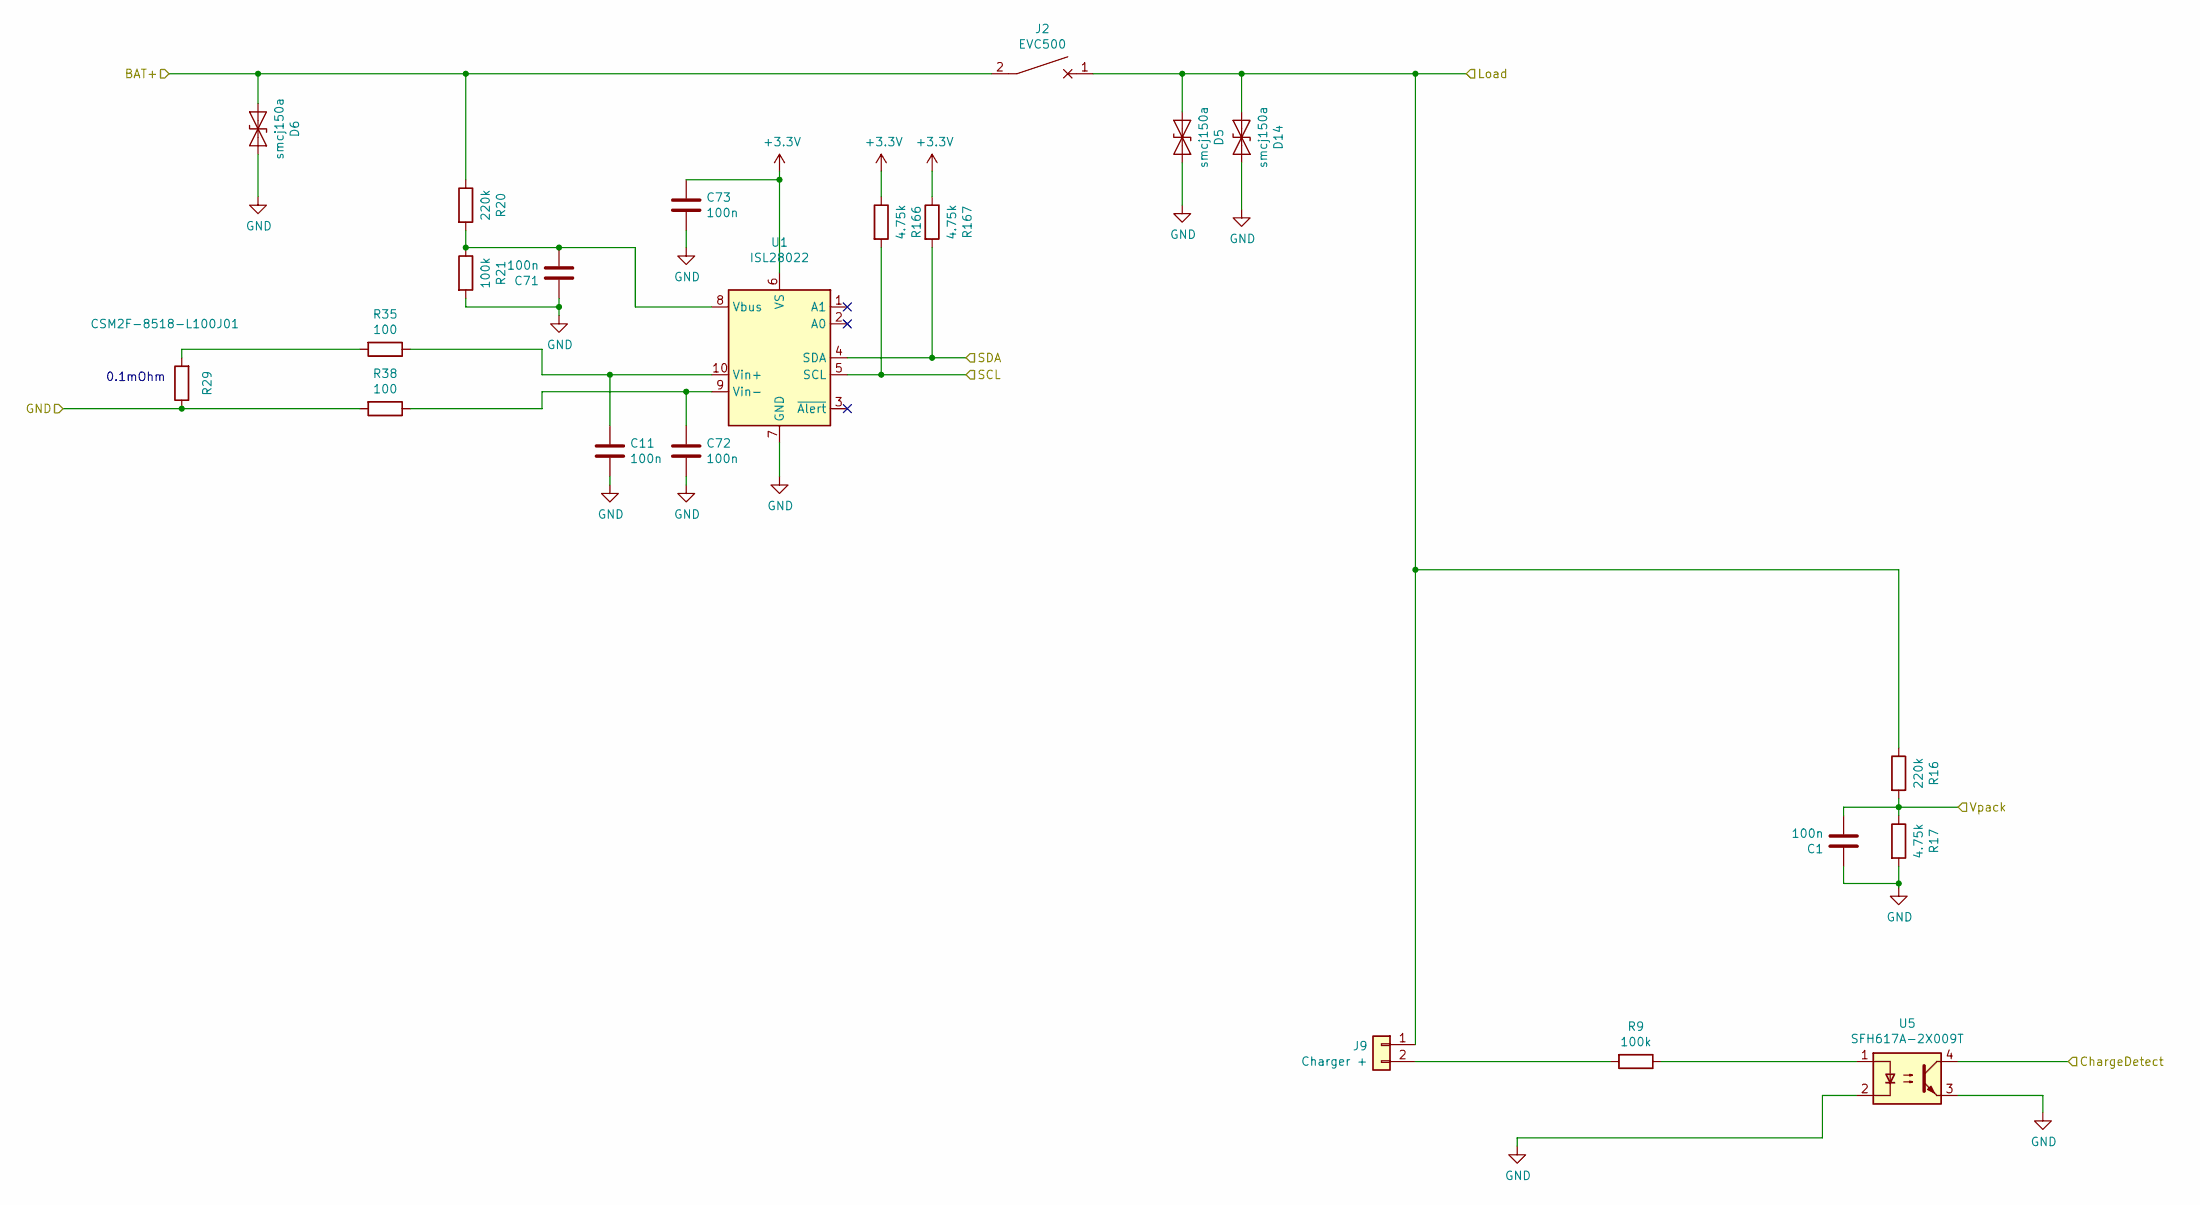
[picture p27: schematic PowerMonitor.sch]

Parts:
C1, C11, C71, C72, C73: 100n; C_0603_1608Metric; MPN GRM188R71E104KA01D
D5, D6, D14: smcj150a; D_SMC
J2: EVC500; MPN N/A
J9: Charger +; PhoenixContact_MCV_1,5_2-G-5.08_1x02_P5.08mm_Vertical; MPN 30.102
R9: 100k; R_2512_6332Metric; MPN RC2512FK-07100KL
R16, R20: 220k; R_2512_6332Metric; MPN 25121WF2203T4E
R17, R166, R167: 4.75k; R_0603_1608Metric; MPN RC0603JR-074K7L
R21: 100k; R_0603_1608Metric; MPN RC0603JR-07100KL
R29: CSM2F-8518-L100J01; MPN CSM2F-8518-L100J01
R35, R38: 100; R_0603_1608Metric; MPN RC0603FR-07100RL
U1: ISL28022; VSSOP-10_3x3mm_P0.5mm; MPN ISL28022FUZ-T7A
U5: SFH617A-2X009T; SMDIP-4_W9.53mm_Clearance8mm; MPN SFH617A-2X009T

Connections:
+3.3V: C73.2, R166.1, R167.1, U1.6 (VS)
BAT+: D6.1 (A1), J2.2, R20.1
ChargeDetect: U5.4
GND: C1.2, C11.1, C71.2, C72.1, C73.1, D5.2 (A2), D6.2 (A2), D14.2 (A2), R17.2, R21.2, R29.1, R38.2, U1.7 (GND), U5.2, U5.3
Load: D5.1 (A1), D14.1 (A1), J2.1, J9.1, R16.1
unnamed: C11.2, R35.1, U1.10 (Vin+)
unnamed: C71.1, R20.2, R21.1, U1.8 (Vbus)
unnamed: C72.2, R38.1, U1.9 (Vin-)
unnamed: J9.2, R9.2
unnamed: R9.1, U5.1
unnamed: R29.2, R35.2
SCL: R166.2, U1.5 (SCL)
SDA: R167.2, U1.4 (SDA)
Vpack: C1.1, R16.2, R17.1

Notes on the sheet:
0.1mOhm
