EnnoidMe/ENNOID-BMS/Master/LV/PCB/switches.sch

## KiCad design Master/LV/PCB/switches.sch (2020-03-01)

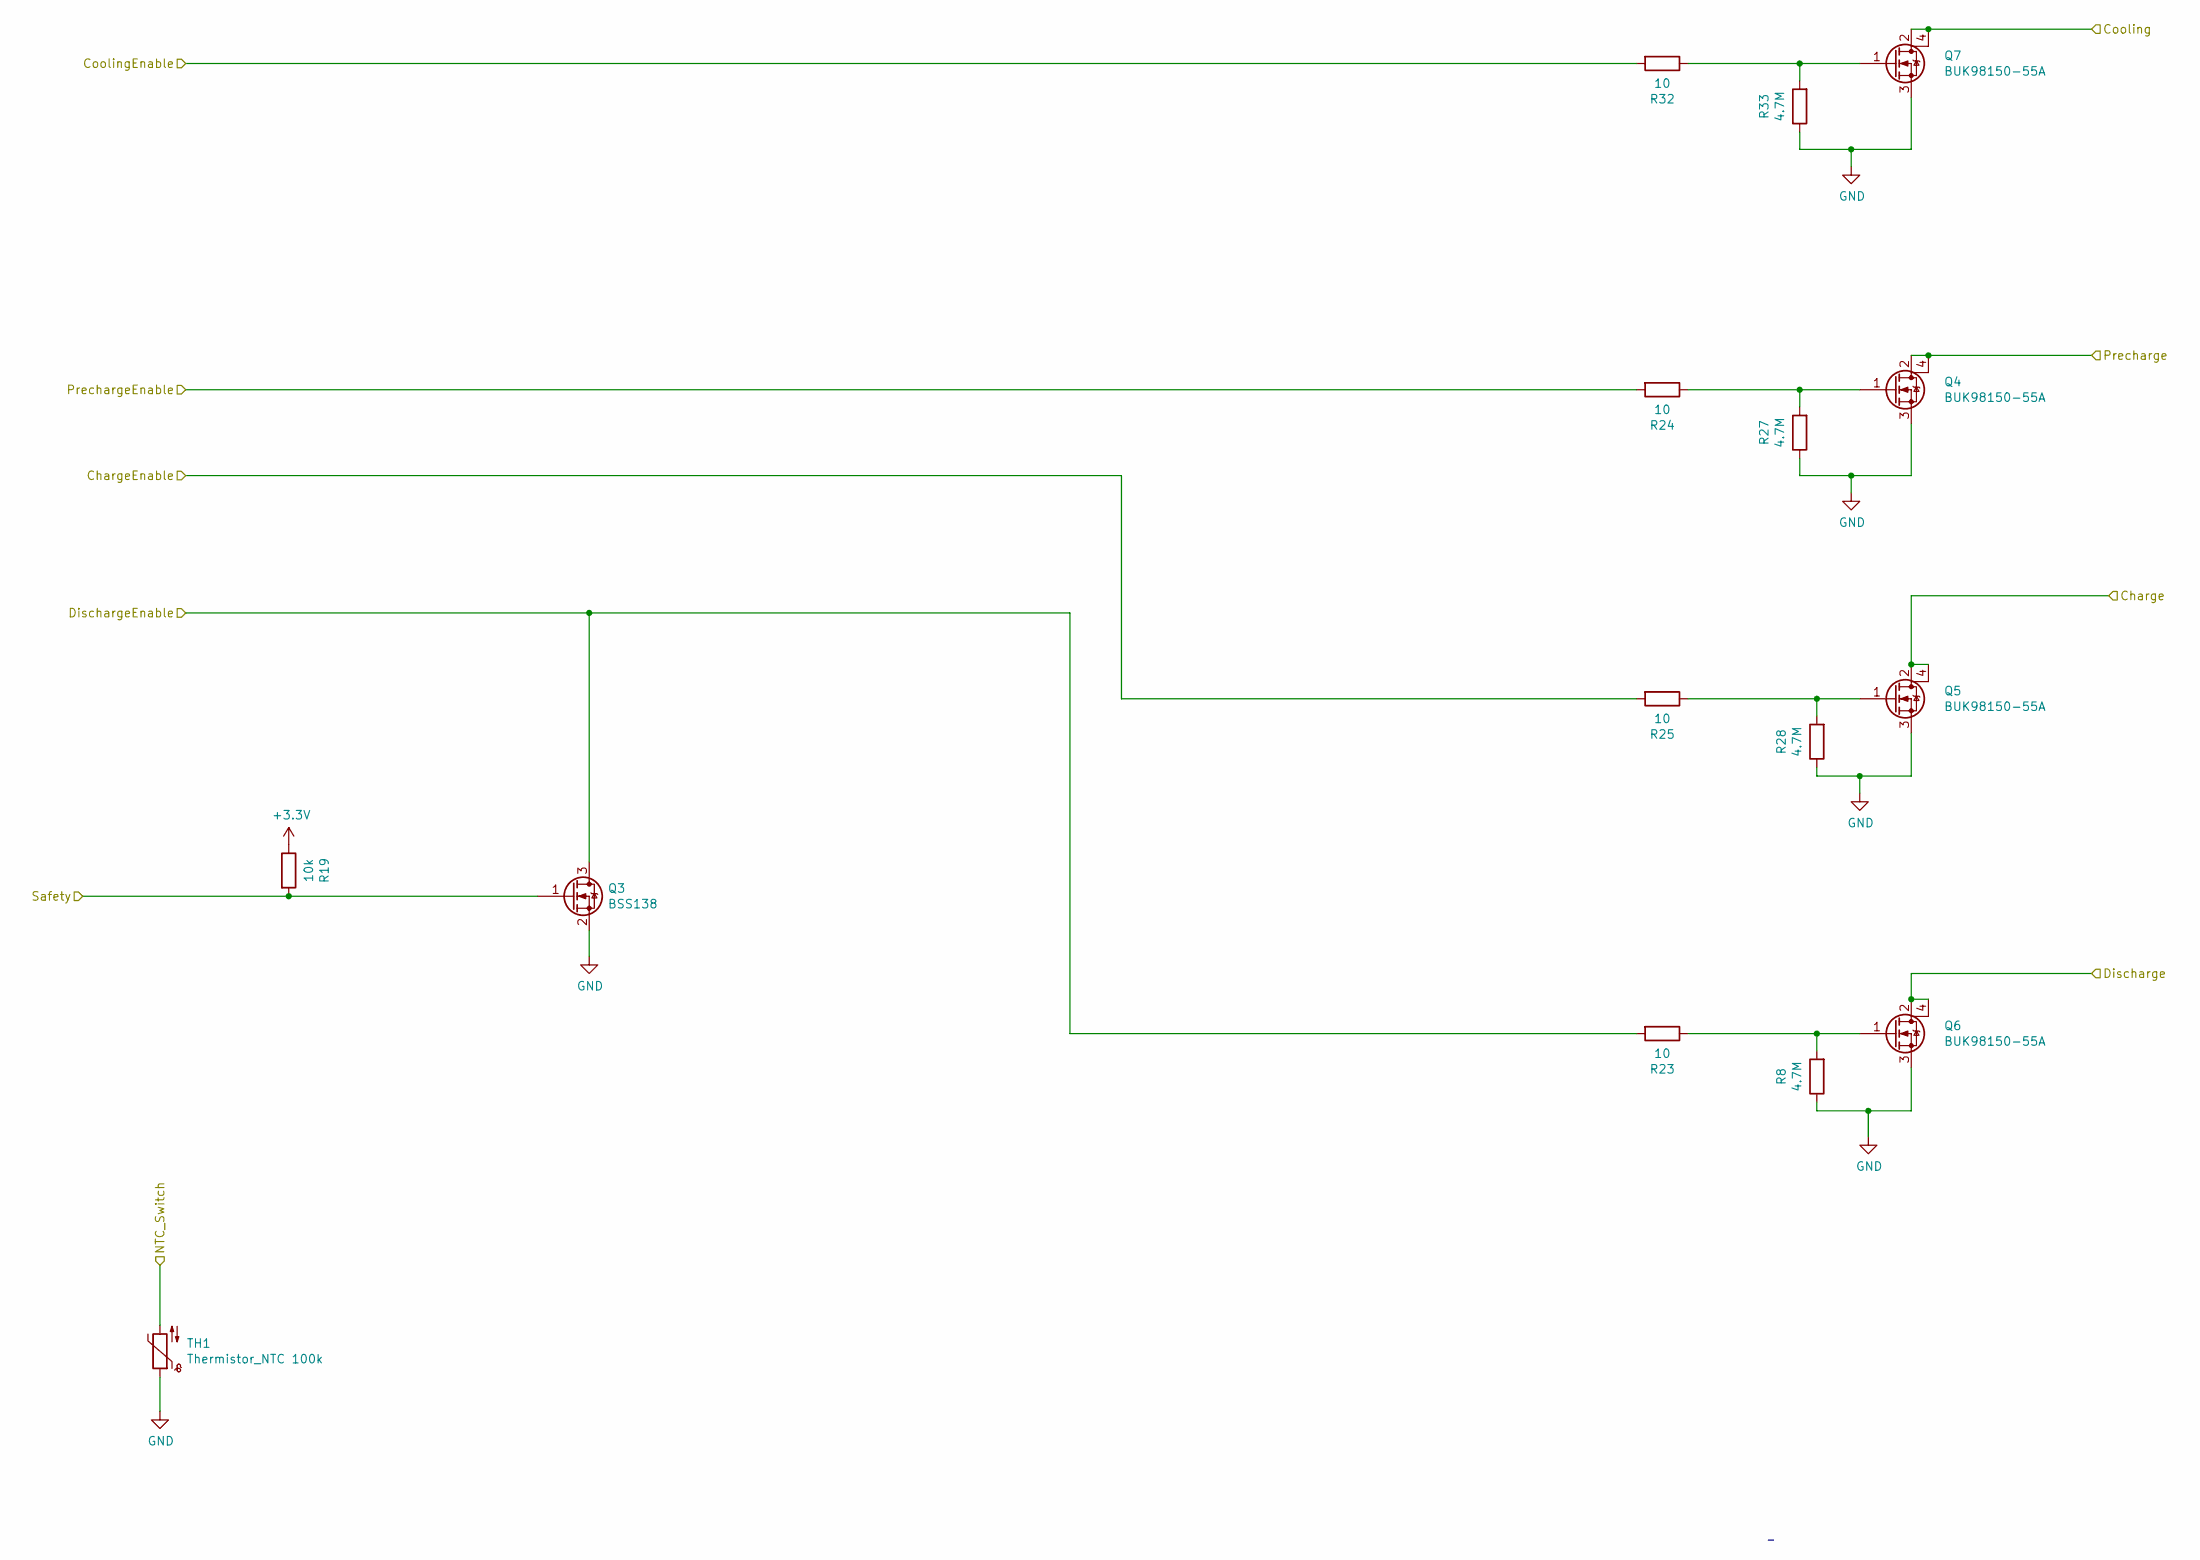
[picture p28: schematic switches.sch]

Parts:
Q3: BSS138; SOT-23; MPN BSS138
Q4, Q5, Q6, Q7: BUK98150-55A; SOT-223; MPN BUK98150-55A/CUF
R8, R27, R28, R33: 4.7M; R_0603_1608Metric; MPN RC0603FR-074M7L
R19: 10k; R_0603_1608Metric; MPN RMCF2512JT10K0
R23, R24, R25, R32: 10; R_0603_1608Metric; MPN RC0603JR-0710RL
TH1: Thermistor_NTC 100k; R_0805_2012Metric; MPN SDNT2012X104F4250FTF

Connections:
+3.3V: R19.1
Charge: Q5.2 (D), Q5.4 (D)
ChargeEnable: R25.2
Cooling: Q7.2 (D), Q7.4 (D)
CoolingEnable: R32.2
Discharge: Q6.2 (D), Q6.4 (D)
DischargeEnable: Q3.3 (D), R23.2
GND: Q3.2 (S), Q4.3 (S), Q5.3 (S), Q6.3 (S), Q7.3 (S), R8.1, R27.1, R28.1, R33.1, TH1.1
NTC_Switch: TH1.2
unnamed: Q4.1 (G), R24.1, R27.2
unnamed: Q5.1 (G), R25.1, R28.2
unnamed: Q6.1 (G), R8.2, R23.1
unnamed: Q7.1 (G), R32.1, R33.2
Precharge: Q4.2 (D), Q4.4 (D)
PrechargeEnable: R24.2
Safety: Q3.1 (G), R19.2
