EnnoidMe/ENNOID-BMS/Slaves/LTC6811/12W/PCB/cell.sch

## KiCad design Slaves/LTC6811/12W/PCB/cell.sch (2020-03-01)

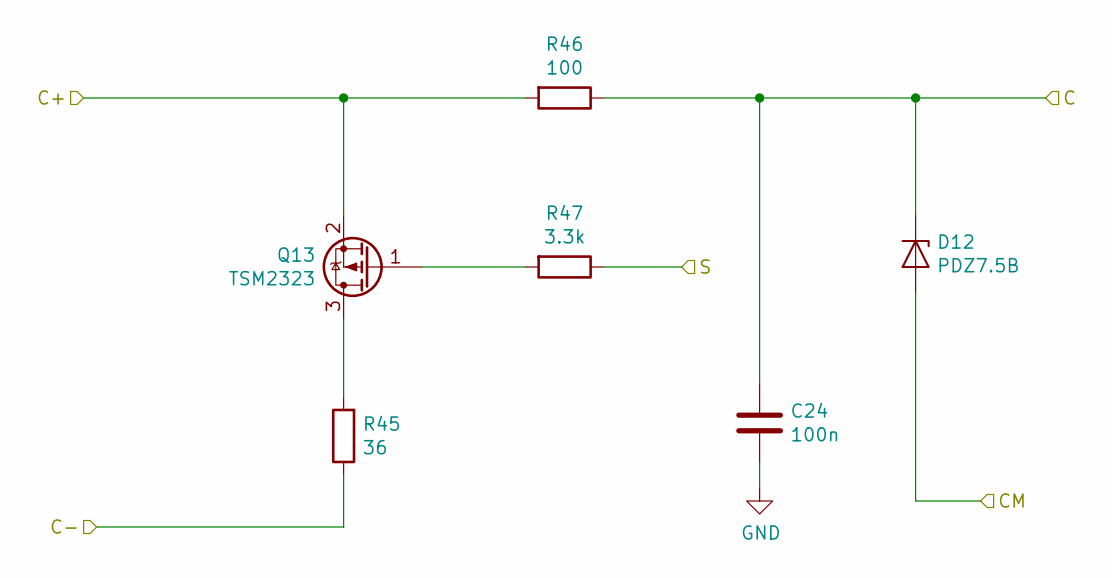
[picture p30: schematic cell.sch]

Parts:
C13: 100n; C_0603_1608Metric; MPN CC0603KRX7R0BB104
D1: PDZ7.5B; D_SOD-323; MPN PDZ7.5BZ
Q2: TSM2323; SOT-23; MPN TSM2323CX RFG
R12: 36; R_2512_6332Metric; MPN RTT25360JTE
R13: 100; R_0603_1608Metric; MPN RC0603FR-07100RL
R14: 3.3k; R_0603_1608Metric; MPN RC0603JR-073K3L

Connections:
C: C13.1, D1.1 (K), R13.1
C+: Q2.2 (S), R13.2
C-: R12.1
CM: D1.2 (A)
GND: C13.2
unnamed: Q2.1 (G), R14.2
unnamed: Q2.3 (D), R12.2
S: R14.1
