EnnoidMe/ENNOID-BMS/Slaves/LTC6811/24W/PCB/LTC6811.sch

## KiCad design Slaves/LTC6811/24W/PCB/LTC6811.sch (2019-11-30)

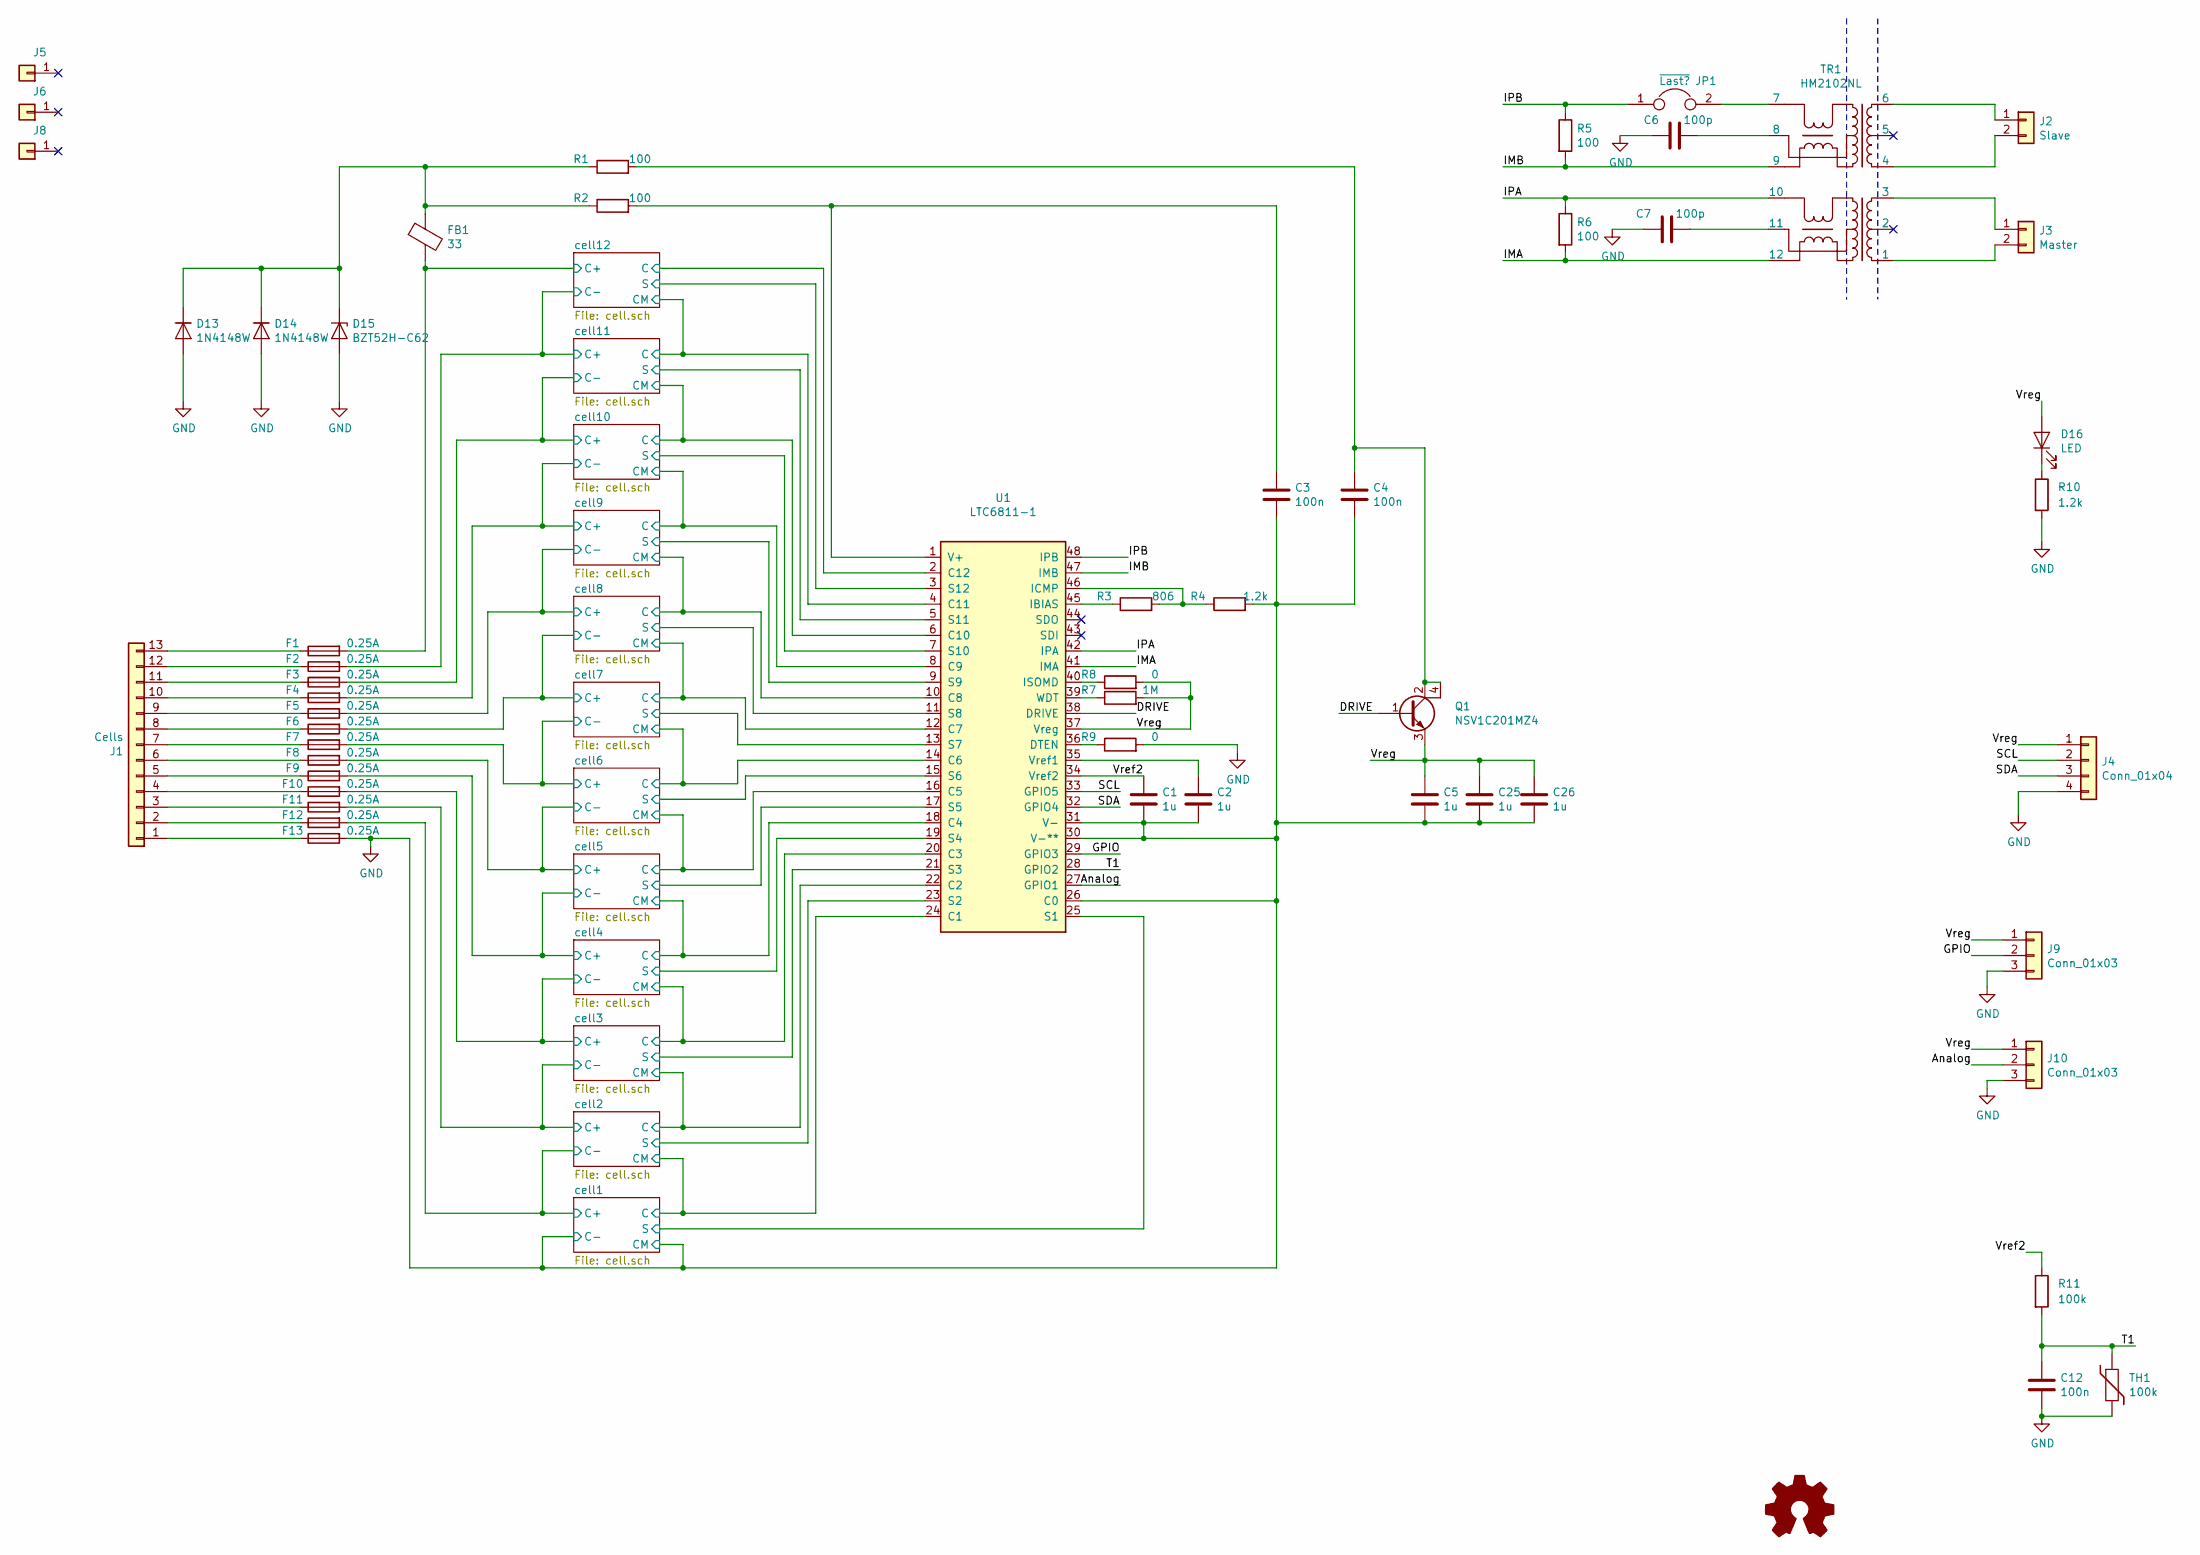
[picture p31: schematic LTC6811.sch]

Parts:
C1, C2, C5, C25, C26: 1u; C_0805_HandSoldering
C3, C4, C12: 100n; C_0603_HandSoldering
C6, C7: 100p; C_0603_HandSoldering
D13, D14: 1N4148W; D_SOD-123
D15: BZT52H-C62; D_SOD-123
D16: LED; LED_0603_1608Metric_Pad1.05x0.95mm_HandSolder
F1, F2, F3, F4, F5, F6, F7, F8, F9, F10, F11, F12, F13: 0.25A; FUSE; MPN N/A
FB1: 33; R_0603_HandSoldering
J1: Cells; Pin_Header_Angled_1x13_Pitch2.54mm
J2: Slave; Molex_KK-6410-02_02x2.54mm_Straight
J3: Master; Molex_KK-6410-02_02x2.54mm_Straight
J4: Conn_01x04; Pin_Header_Angled_1x04_Pitch2.54mm
J5, J6, J8: Conn_01x01; MountingHole_2.7mm_M2.5_Pad_Via
J9, J10: Conn_01x03; Pin_Header_Angled_1x03_Pitch2.54mm
JP1: ~Last?; Pin_Header_Straight_1x02_Pitch2.54mm
LOGO1: Logo_Open_Hardware_Small; ENNOID-LOGO
Q1: NSV1C201MZ4; SOT-223
R1: 100; R_0603_HandSoldering; MPN RC0603FR-07100RL
R2, R5, R6: 100; R_0603_HandSoldering
R3: 806; R_0603_HandSoldering
R4, R10: 1.2k; R_0603_HandSoldering
R7: 1M; R_0603_HandSoldering
R8, R9: 0; R_0603_HandSoldering
R11: 100k; R_0603_HandSoldering
TH1: 100k; R_0805_HandSoldering
TR1: HM2102NL
U1: LTC6811-1; TSSOP-48_6.1x12.5mm_Pitch0.5mm

Connections:
Analog: J10.2, U1.27 (GPIO1)
C: U1.2 (C12), U1.22 (C2)
C+: F1.2, F11.2, FB1.2
C-: F2.2, F3.2, F4.2, F5.2, F6.2, F7.2, F8.2, F9.2, F10.2, F12.2
CM: U1.4 (C11), U1.6 (C10), U1.8 (C9), U1.10 (C8), U1.12 (C7), U1.14 (C6), U1.16 (C5), U1.18 (C4), U1.20 (C3), U1.24 (C1)
DRIVE: Q1.1 (B), U1.38 (DRIVE)
GND: C1.2, C2.2, C3.2, C4.2, C5.2, C6.2, C7.2, C12.2, C25.2, C26.2, D13.2 (A), D14.2 (A), D15.2 (A), F13.2, J4.4, J9.3, J10.3, R4.2, R9.2, R10.2, TH1.2, U1.26 (C0), U1.30 (V-**), U1.31 (V-)
GPIO: J9.2, U1.29 (GPIO3)
IMA: R6.2, TR1.12, U1.41 (IMA)
IMB: R5.2, TR1.9, U1.47 (IMB)
IPA: R6.1, TR1.10, U1.42 (IPA)
IPB: JP1.1, R5.1, U1.48 (IPB)
unnamed: C2.1, U1.35 (Vref1)
unnamed: C3.1, R2.2, U1.1 (V+)
unnamed: C4.1, Q1.2 (C), Q1.4 (C), R1.2
unnamed: C6.1, TR1.8
unnamed: C7.1, TR1.11
unnamed: D13.1 (K), D14.1 (K), D15.1 (K), FB1.1, R1.1, R2.1
unnamed: D16.1 (K), R10.1
unnamed: F1.1, J1.13
unnamed: F2.1, J1.12
unnamed: F3.1, J1.11
unnamed: F4.1, J1.10
unnamed: F5.1, J1.9
unnamed: F6.1, J1.8
unnamed: F7.1, J1.7
unnamed: F8.1, J1.6
unnamed: F9.1, J1.5
unnamed: F10.1, J1.4
unnamed: F11.1, J1.3
unnamed: F12.1, J1.2
unnamed: F13.1, J1.1
unnamed: J2.1, TR1.6
unnamed: J2.2, TR1.4
unnamed: J3.1, TR1.3
unnamed: J3.2, TR1.1
unnamed: JP1.2, TR1.7
unnamed: R3.1, U1.45 (IBIAS)
unnamed: R3.2, R4.1, U1.46 (ICMP)
unnamed: R7.1, U1.39 (WDT)
unnamed: R8.1, U1.40 (ISOMD)
unnamed: R9.1, U1.36 (DTEN)
S: U1.3 (S12), U1.5 (S11), U1.7 (S10), U1.9 (S9), U1.11 (S8), U1.13 (S7), U1.15 (S6), U1.17 (S5), U1.19 (S4), U1.21 (S3), U1.23 (S2), U1.25 (S1)
SCL: J4.2, U1.33 (GPIO5)
SDA: J4.3, U1.32 (GPIO4)
T1: C12.1, R11.2, TH1.1, U1.28 (GPIO2)
Vref2: C1.1, R11.1, U1.34 (Vref2)
Vreg: C5.1, C25.1, C26.1, D16.2 (A), J4.1, J9.1, J10.1, Q1.3 (E), R7.2, R8.2, U1.37 (Vreg)
