EnnoidMe/ENNOID-BMS/Slaves/LTC6811/24W/PCB/cell.sch

## KiCad design Slaves/LTC6811/24W/PCB/cell.sch (2019-09-12)

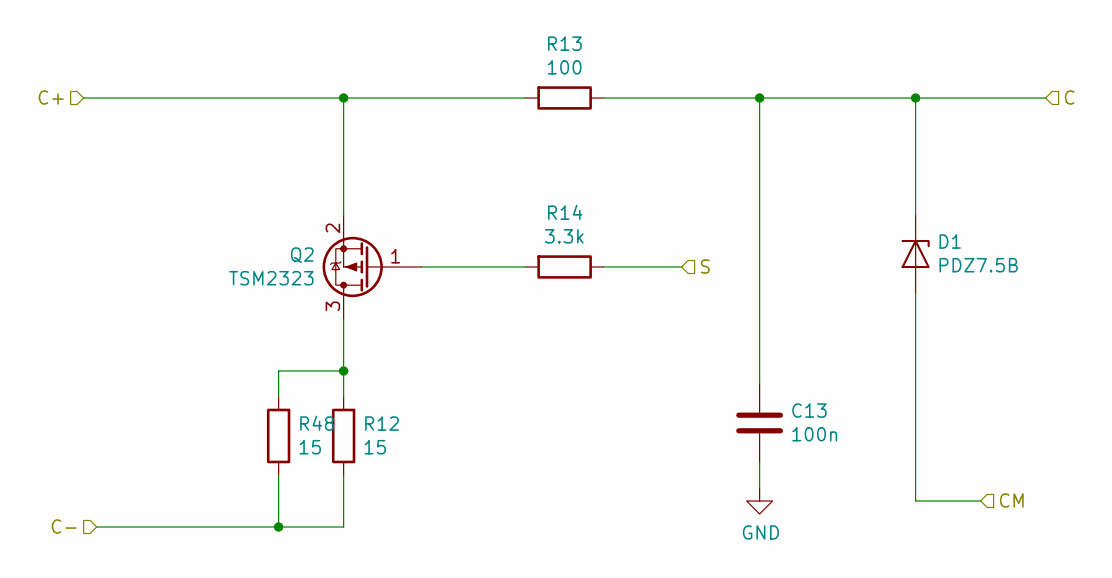
[picture p32: schematic cell.sch]

Parts:
C13: 100n; C_0805_HandSoldering
D1: PDZ7.5B; D_SOD-323_HandSoldering
Q2: TSM2323; SOT-23
R12, R48: 15; R_2512
R13: 100; R_0603_HandSoldering
R14: 3.3k; R_0603_HandSoldering

Connections:
C: C13.1, D1.1 (K), R13.1
C+: Q2.2 (S), R13.2
C-: R12.1, R48.1
CM: D1.2 (A)
GND: C13.2
unnamed: Q2.1 (G), R14.2
unnamed: Q2.3 (D), R12.2, R48.2
S: R14.1
