EnnoidMe/ENNOID-BMS/Slaves/LTC6812/15W/PCB/LTC6812-15W.sch

## KiCad design Slaves/LTC6812/15W/PCB/LTC6812-15W.sch (2020-03-01)

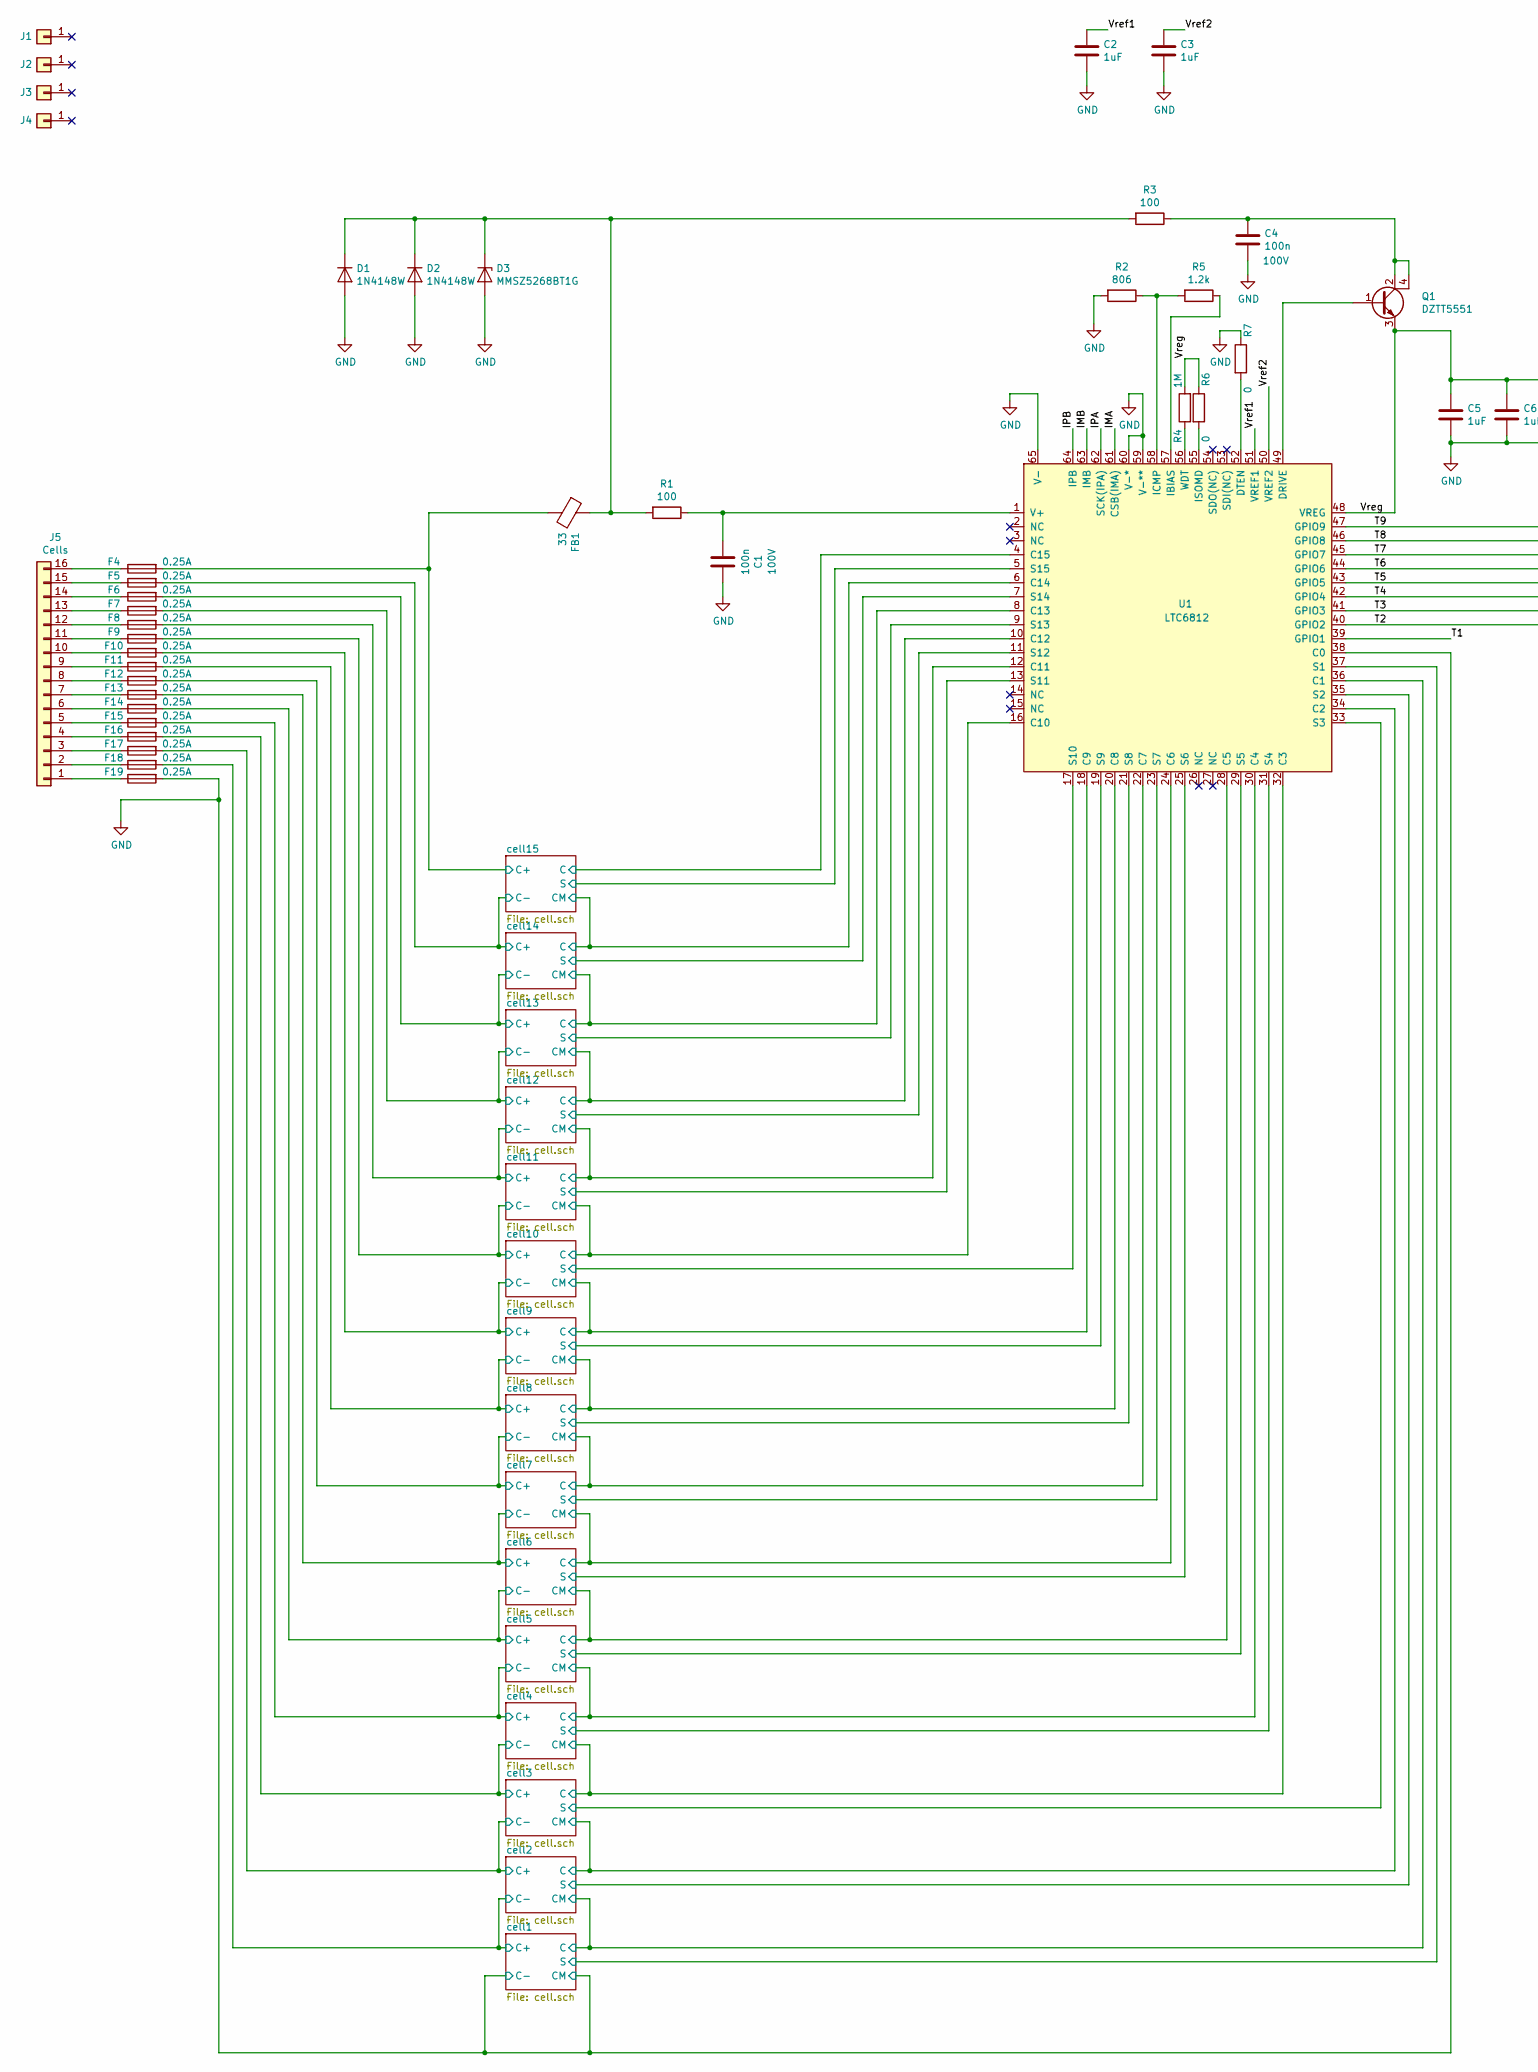
[picture p33: schematic LTC6812-15W.sch, part in row 1, column 1]

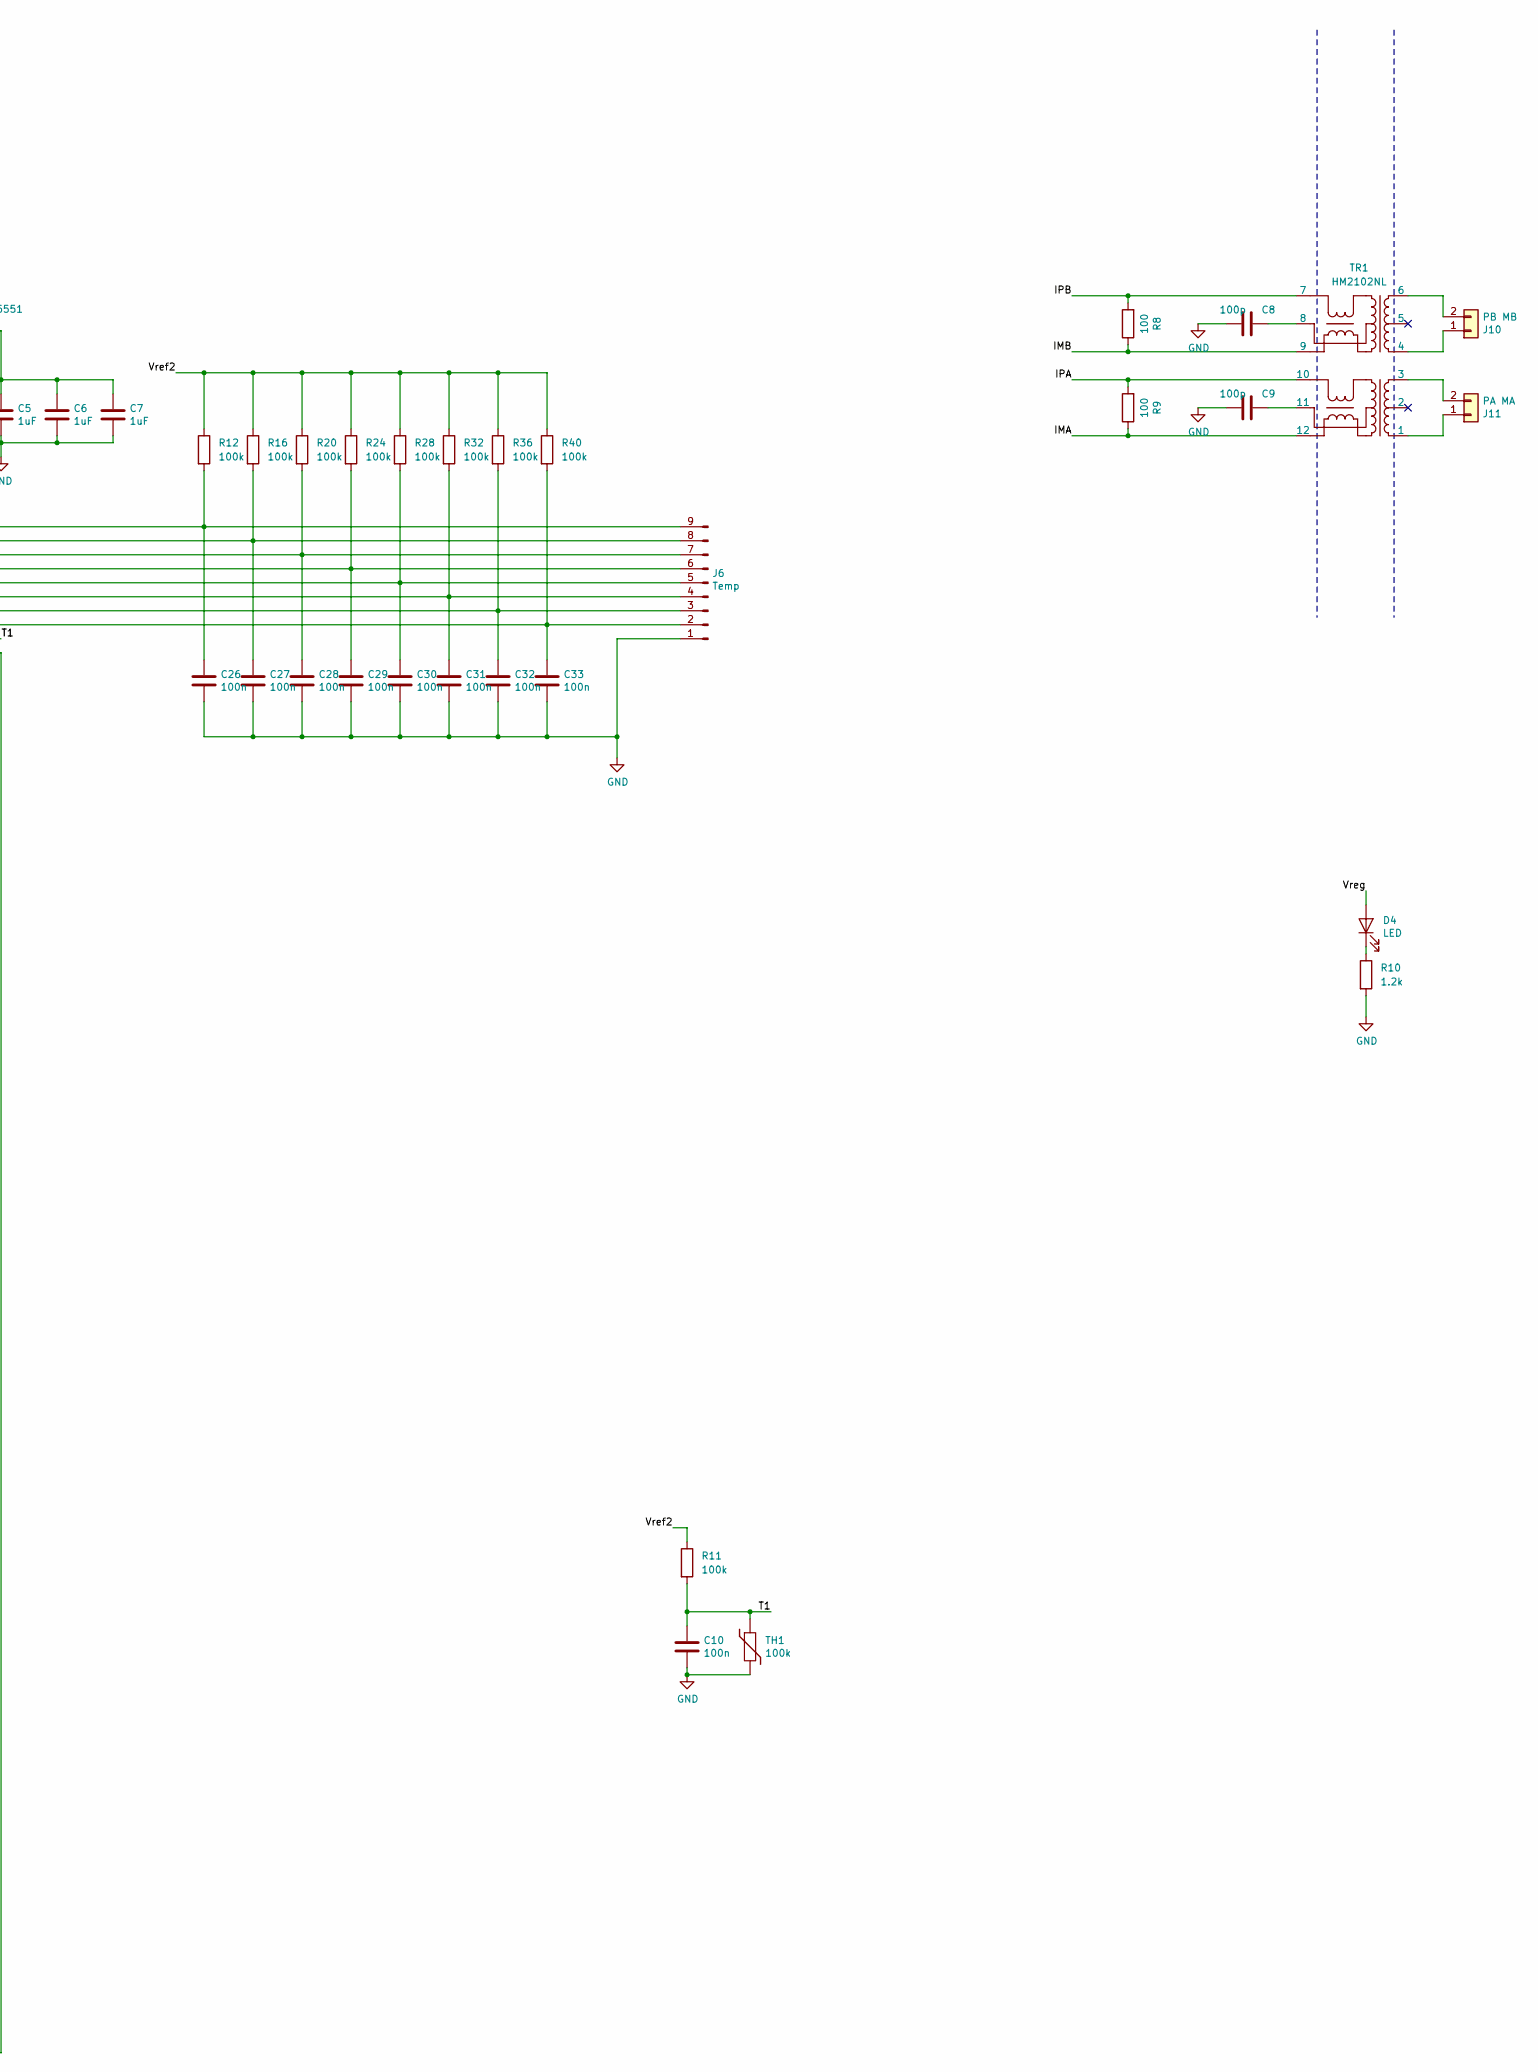
[picture p34: schematic LTC6812-15W.sch, part in row 1, column 2]

Parts:
C1, C4: 100n; C_0603_1608Metric; Voltage 100V; MPN GRM188R72A104KA35D
C2, C3, C5, C6, C7: 1uF; C_0603_1608Metric; MPN CL10B105KP8NNNC
C8, C9: 100p; C_0603_1608Metric; MPN GRM1885C1H101JA01D
C10, C26, C27, C28, C29, C30, C31, C32, C33: 100n; C_0603_1608Metric; MPN GRM188R72A104KA35D
D1, D2: 1N4148W; D_SOD-123; MPN 1N4148W-7-F
D3: MMSZ5268BT1G; D_SOD-123; MPN MMSZ5268BT1G
D4: LED; LED_0603_1608Metric_Pad1.05x0.95mm_HandSolder
F4, F5, F6, F7, F8, F9, F10, F11, F12, F13, F14, F15, F16, F17, F18, F19: 0.25A; FUSE
FB1: 33; R_0603_1608Metric; MPN BLM18PG330SN1D
J1, J2, J3, J4: Conn_01x01; MountingHole_3.2mm_M3_ISO7380_Pad
J5: Cells; Pin_Header_Angled_1x16_Pitch2.54mm
J6: Temp; PinHeader_1x09_P2.54mm_Horizontal
J10: PB MB; Pin_1x02-XL
J11: PA MA; Pin_1x02-XL
Q1: DZTT5551; SOT-223; MPN DZT5551-13
R1, R3, R8, R9: 100; R_0603_1608Metric
R2: 806; R_0603_1608Metric
R4: 1M; R_0603_1608Metric
R5, R10: 1.2k; R_0603_1608Metric
R6, R7: 0; R_0603_1608Metric
R11, R12, R16, R20, R24, R28, R32, R36, R40: 100k; R_0603_1608Metric
TH1: 100k; R_0805_2012Metric
TR1: HM2102NL
U1: LTC6812; TQFP-64-1EP_10x10mm_P0.5mm_EP8x8mm

Connections:
C: U1.4 (C15), U1.6 (C14), U1.8 (C13), U1.10 (C12), U1.12 (C11), U1.18 (C9), U1.20 (C8), U1.22 (C7), U1.24 (C6), U1.28 (C5), U1.30 (C4), U1.32 (C3), U1.34 (C2), U1.36 (C1)
C+: F4.2, F5.2, F6.2, F7.2, F8.2, F10.2, F11.2, F12.2, F13.2, F14.2, F15.2, F16.2, F17.2, F18.2, FB1.2
C-: F9.2
CM: U1.16 (C10)
GND: C1.1, C2.1, C3.1, C4.1, C5.1, C6.1, C7.1, C8.1, C9.1, C10.2, C26.2, C27.2, C28.2, C29.2, C30.2, C31.2, C32.2, C33.2, D1.2 (A), D2.2 (A), D3.2 (A), F19.2, J6.1, R2.2, R7.1, R10.2, TH1.2, U1.38 (C0), U1.59 (V-**), U1.60 (V-*), U1.65 (V-)
IMA: R9.1, TR1.12, U1.61 (CSB(IMA))
IMB: R8.1, TR1.9, U1.63 (IMB)
IPA: R9.2, TR1.10, U1.62 (SCK(IPA))
IPB: R8.2, TR1.7, U1.64 (IPB)
unnamed: C1.2, R1.1, U1.1 (V+)
unnamed: C4.2, Q1.2 (C), Q1.4 (C), R3.1
unnamed: C8.2, TR1.8
unnamed: C9.2, TR1.11
unnamed: D1.1 (K), D2.1 (K), D3.1 (K), FB1.1, R1.2, R3.2
unnamed: D4.1 (K), R10.1
unnamed: F4.1, J5.16
unnamed: F5.1, J5.15
unnamed: F6.1, J5.14
unnamed: F7.1, J5.13
unnamed: F8.1, J5.12
unnamed: F9.1, J5.11
unnamed: F10.1, J5.10
unnamed: F11.1, J5.9
unnamed: F12.1, J5.8
unnamed: F13.1, J5.7
unnamed: F14.1, J5.6
unnamed: F15.1, J5.5
unnamed: F16.1, J5.4
unnamed: F17.1, J5.3
unnamed: F18.1, J5.2
unnamed: F19.1, J5.1
unnamed: J10.1, TR1.4
unnamed: J10.2, TR1.6
unnamed: J11.1, TR1.1
unnamed: J11.2, TR1.3
unnamed: Q1.1 (B), U1.49 (DRIVE)
unnamed: R2.1, R5.2, U1.58 (ICMP)
unnamed: R4.1, U1.56 (WDT)
unnamed: R5.1, U1.57 (IBIAS)
unnamed: R6.2, U1.55 (ISOMD)
unnamed: R7.2, U1.52 (DTEN)
S: U1.5 (S15), U1.7 (S14), U1.9 (S13), U1.11 (S12), U1.13 (S11), U1.17 (S10), U1.19 (S9), U1.21 (S8), U1.23 (S7), U1.25 (S6), U1.29 (S5), U1.31 (S4), U1.33 (S3), U1.35 (S2), U1.37 (S1)
T1: C10.1, R11.2, TH1.1, U1.39 (GPIO1)
T2: C33.1, J6.2, R40.2, U1.40 (GPIO2)
T3: C32.1, J6.3, R36.2, U1.41 (GPIO3)
T4: C31.1, J6.4, R32.2, U1.42 (GPIO4)
T5: C30.1, J6.5, R28.2, U1.43 (GPIO5)
T6: C29.1, J6.6, R24.2, U1.44 (GPIO6)
T7: C28.1, J6.7, R20.2, U1.45 (GPIO7)
T8: C27.1, J6.8, R16.2, U1.46 (GPIO8)
T9: C26.1, J6.9, R12.2, U1.47 (GPIO9)
Vref1: C2.2, U1.51 (VREF1)
Vref2: C3.2, R11.1, R12.1, R16.1, R20.1, R24.1, R28.1, R32.1, R36.1, R40.1, U1.50 (VREF2)
Vreg: C5.2, C6.2, C7.2, D4.2 (A), Q1.3 (E), R4.2, R6.1, U1.48 (VREG)
