EnnoidMe/ENNOID-BMS/Slaves/LTC6812/15W/PCB/cell.sch

## KiCad design Slaves/LTC6812/15W/PCB/cell.sch (2020-02-08)

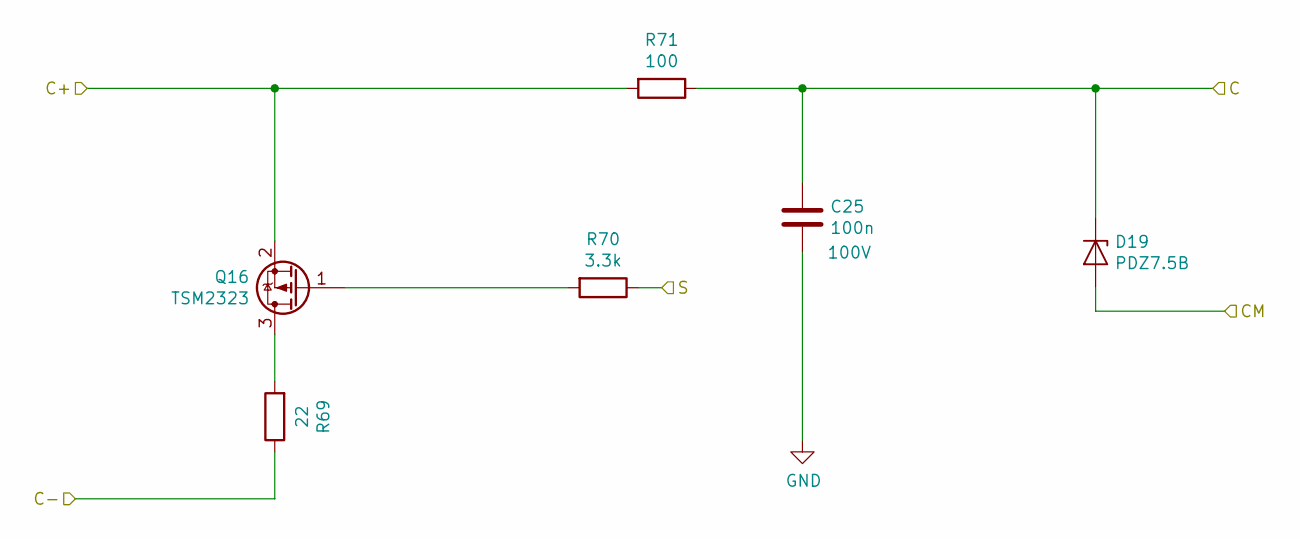
[picture p35: schematic cell.sch]

Parts:
C11: 100n; C_0603_1608Metric; Voltage 100V; MPN GRM188R72A104KA35D
D5: PDZ7.5B; D_SOD-323; MPN PDZ7.5B
Q2: TSM2323; SOT-23
R13: 22; R_2512_6332Metric
R14: 3.3k; R_0603_1608Metric
R15: 100; R_0603_1608Metric

Connections:
C: C11.2, D5.1 (K), R15.1
C+: Q2.2 (S), R15.2
C-: R13.1
CM: D5.2 (A)
GND: C11.1
unnamed: Q2.1 (G), R14.2
unnamed: Q2.3 (D), R13.2
S: R14.1
