EnnoidMe/ENNOID-BMS/Slaves/LTC6812/30W/PCB/LTC6812.sch

## KiCad design Slaves/LTC6812/30W/PCB/LTC6812.sch (2019-09-04)

Schematic: LTC6812.sch

Parts:
C1, C4: 100nF; C_0603_HandSoldering; Voltage 100V
C2, C3, C5, C6, C7: 1uF; C_0603_HandSoldering
C8, C9: 100p; C_0603_HandSoldering
C10: 100n; C_0603_HandSoldering
D1, D2: 1N4148W; D_SOD-123
D3: BZT52H-C62; D_SOD-123
D4: LED; LED_0603_1608Metric_Pad1.05x0.95mm_HandSolder
F4, F5, F6, F7, F8, F9, F10, F11, F12, F13, F14, F15, F16, F17, F18, F19: 0.25A; FUSE
FB1: 33; R_0603_HandSoldering
J1, J2, J3, J4: Conn_01x01; MountingHole_3.2mm_M3_ISO7380_Pad
J5: Cells; Pin_Header_Angled_1x16_Pitch2.54mm
J10: Slave; Molex_KK-6410-02_02x2.54mm_Straight
J11: Master; Molex_KK-6410-02_02x2.54mm_Straight
JP1: ~Last?; Pin_Header_Straight_1x02_Pitch2.54mm
Q1: DZTT5551; SOT-223
R1, R3, R8, R9: 100; R_0603_HandSoldering
R2, R5: 1k; R_0603_HandSoldering
R4: 1M; R_0603_HandSoldering
R6, R7: 0; R_0603_HandSoldering
R10: 1.2k; R_0603_HandSoldering
R11: 100k; R_0603_HandSoldering
TH1: 100k; R_0805_HandSoldering
TR1: HM2102NL
U1: LTC6812; TQFP-64-1EP_10x10mm_Pitch0.5mm
