EnnoidMe/ENNOID-BMS/Slaves/LTC6813/18W/PCB/cell.sch

## KiCad design Slaves/LTC6813/18W/PCB/cell.sch (2019-11-30)

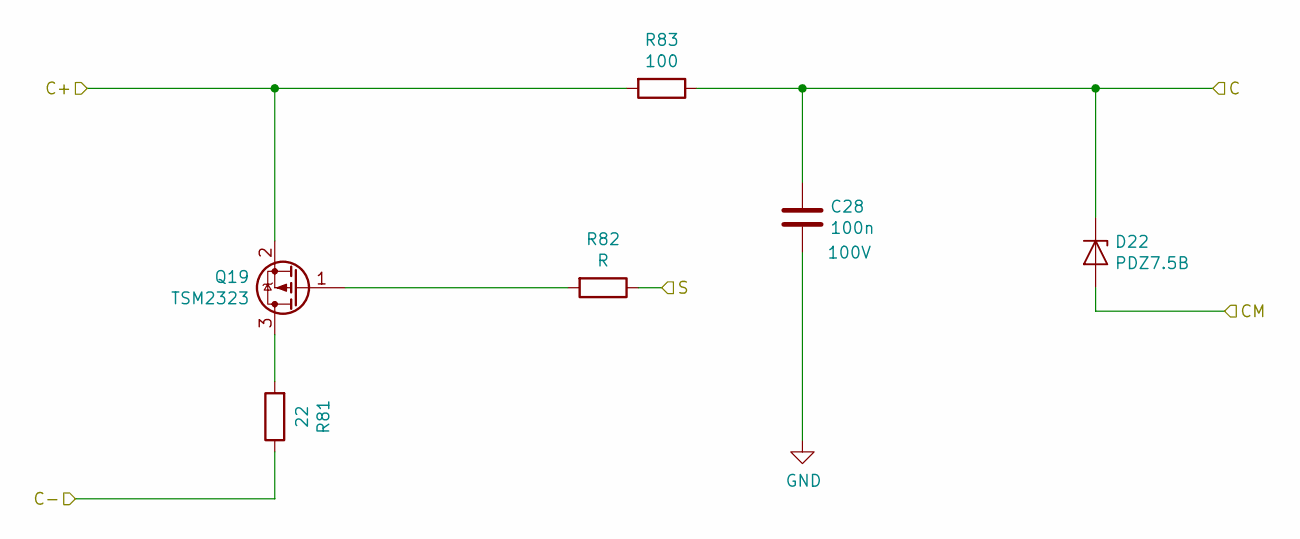
[picture p38: schematic cell.sch]

Parts:
C11: 100n; C_0805_2012Metric; Voltage 100V
D5: PDZ7.5B; D_SOD-323
Q2: TSM2323; SOT-23
R13: 22; R_2512_6332Metric
R14: R; R_0603_1608Metric
R15: 100; R_0603_1608Metric

Connections:
C: C11.2, D5.1 (K), R15.1
C+: Q2.2 (S), R15.2
C-: R13.1
CM: D5.2 (A)
GND: C11.1
unnamed: Q2.1 (G), R14.2
unnamed: Q2.3 (D), R13.2
S: R14.1
