EnnoidMe/ENNOID-BMS/Slaves/LTC6813/36W/PCB/cell.sch

## KiCad design Slaves/LTC6813/36W/PCB/cell.sch (2019-09-02)

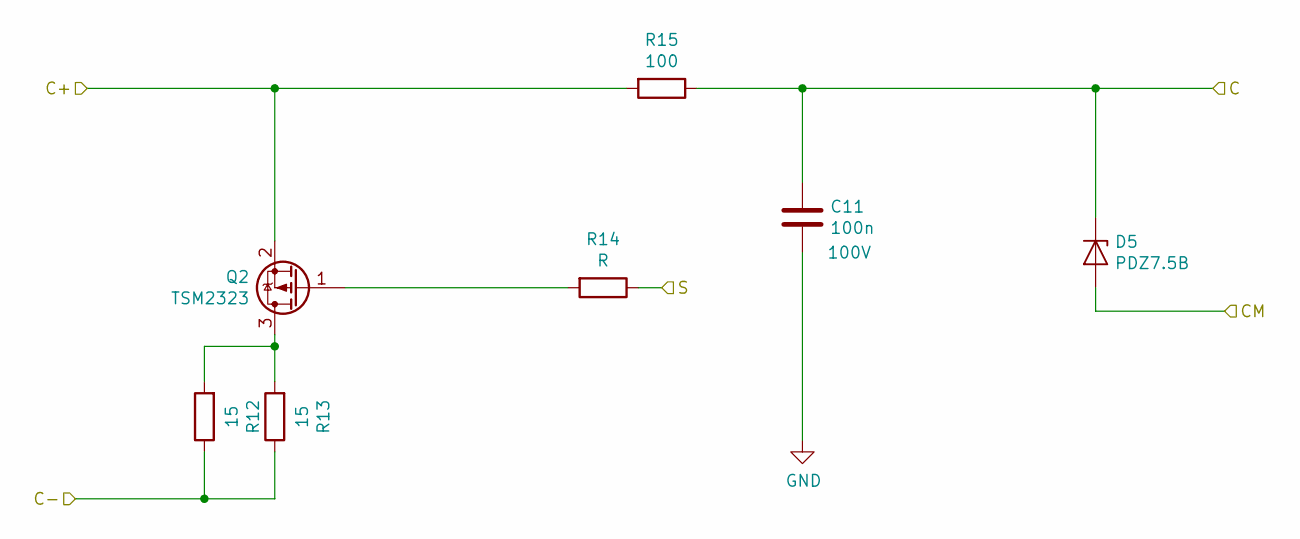
[picture p39: schematic cell.sch]

Parts:
C11: 100n; C_0603_HandSoldering; Voltage 100V
D5: PDZ7.5B; D_SOD-323_HandSoldering
Q2: TSM2323; SOT-23
R12, R13: 15; R_2512
R14: R; R_0603_HandSoldering
R15: 100; R_0603_HandSoldering

Connections:
C: C11.2, D5.1 (K), R15.1
C+: Q2.2 (S), R15.2
C-: R12.1, R13.1
CM: D5.2 (A)
GND: C11.1
unnamed: Q2.1 (G), R14.2
unnamed: Q2.3 (D), R12.2, R13.2
S: R14.1
